schilkp/Fets_and_Crosses/ECAD/EngineTest/EngineTest.sch

## KiCad design ECAD/EngineTest/EngineTest.sch (2021-05-23)

Schematic: EngineTest.sch

Parts:
C1, C2, C3, C4, C7, C9, C10, C11, C12: 0u1; C_0603_1608Metric
C5: 10n; C_0603_1608Metric
C6: 1u; C_0603_1608Metric
C8: 4u7; C_0603_1608Metric
D3: LED; LED_0603_1608Metric
D4: PWR LED; LED_0603_1608Metric
J1: 5V_in; PinHeader_1x02_P2.54mm_Vertical
J2: USB_B_Micro; USB_Mini-B_Wuerth_65100516121_Horizontal
J3: ARM_SWD; PinHeader_2x05_P1.27mm_Vertical
J4: P1; PinSocket_1x10_P2.54mm_Horizontal
J5: P2; PinSocket_1x10_P2.54mm_Horizontal
J6: MOVE; PinSocket_1x10_P2.54mm_Horizontal
J7: PWR; PinSocket_1x10_P2.54mm_Horizontal
JP1: 5V Select; SolderJumper-3_P1.3mm_Open_RoundedPad1.0x1.5mm
R1, R2, R5: 10K; R_0603_1608Metric
R6, R7: rled; R_0603_1608Metric
U1: STM32F030K6Tx; LQFP-32_7x7mm_P0.8mm
U2: FT232RL; SSOP-28_5.3x10.2mm_P0.65mm
U3, U4, U5: 74HCT595PW; TSSOP-16_4.4x5mm_P0.65mm
