schilkp/Fets_and_Crosses/ECAD/Engine/KiCad/Engine.sch

## KiCad design ECAD/Engine/KiCad/Engine.sch (2022-02-07)

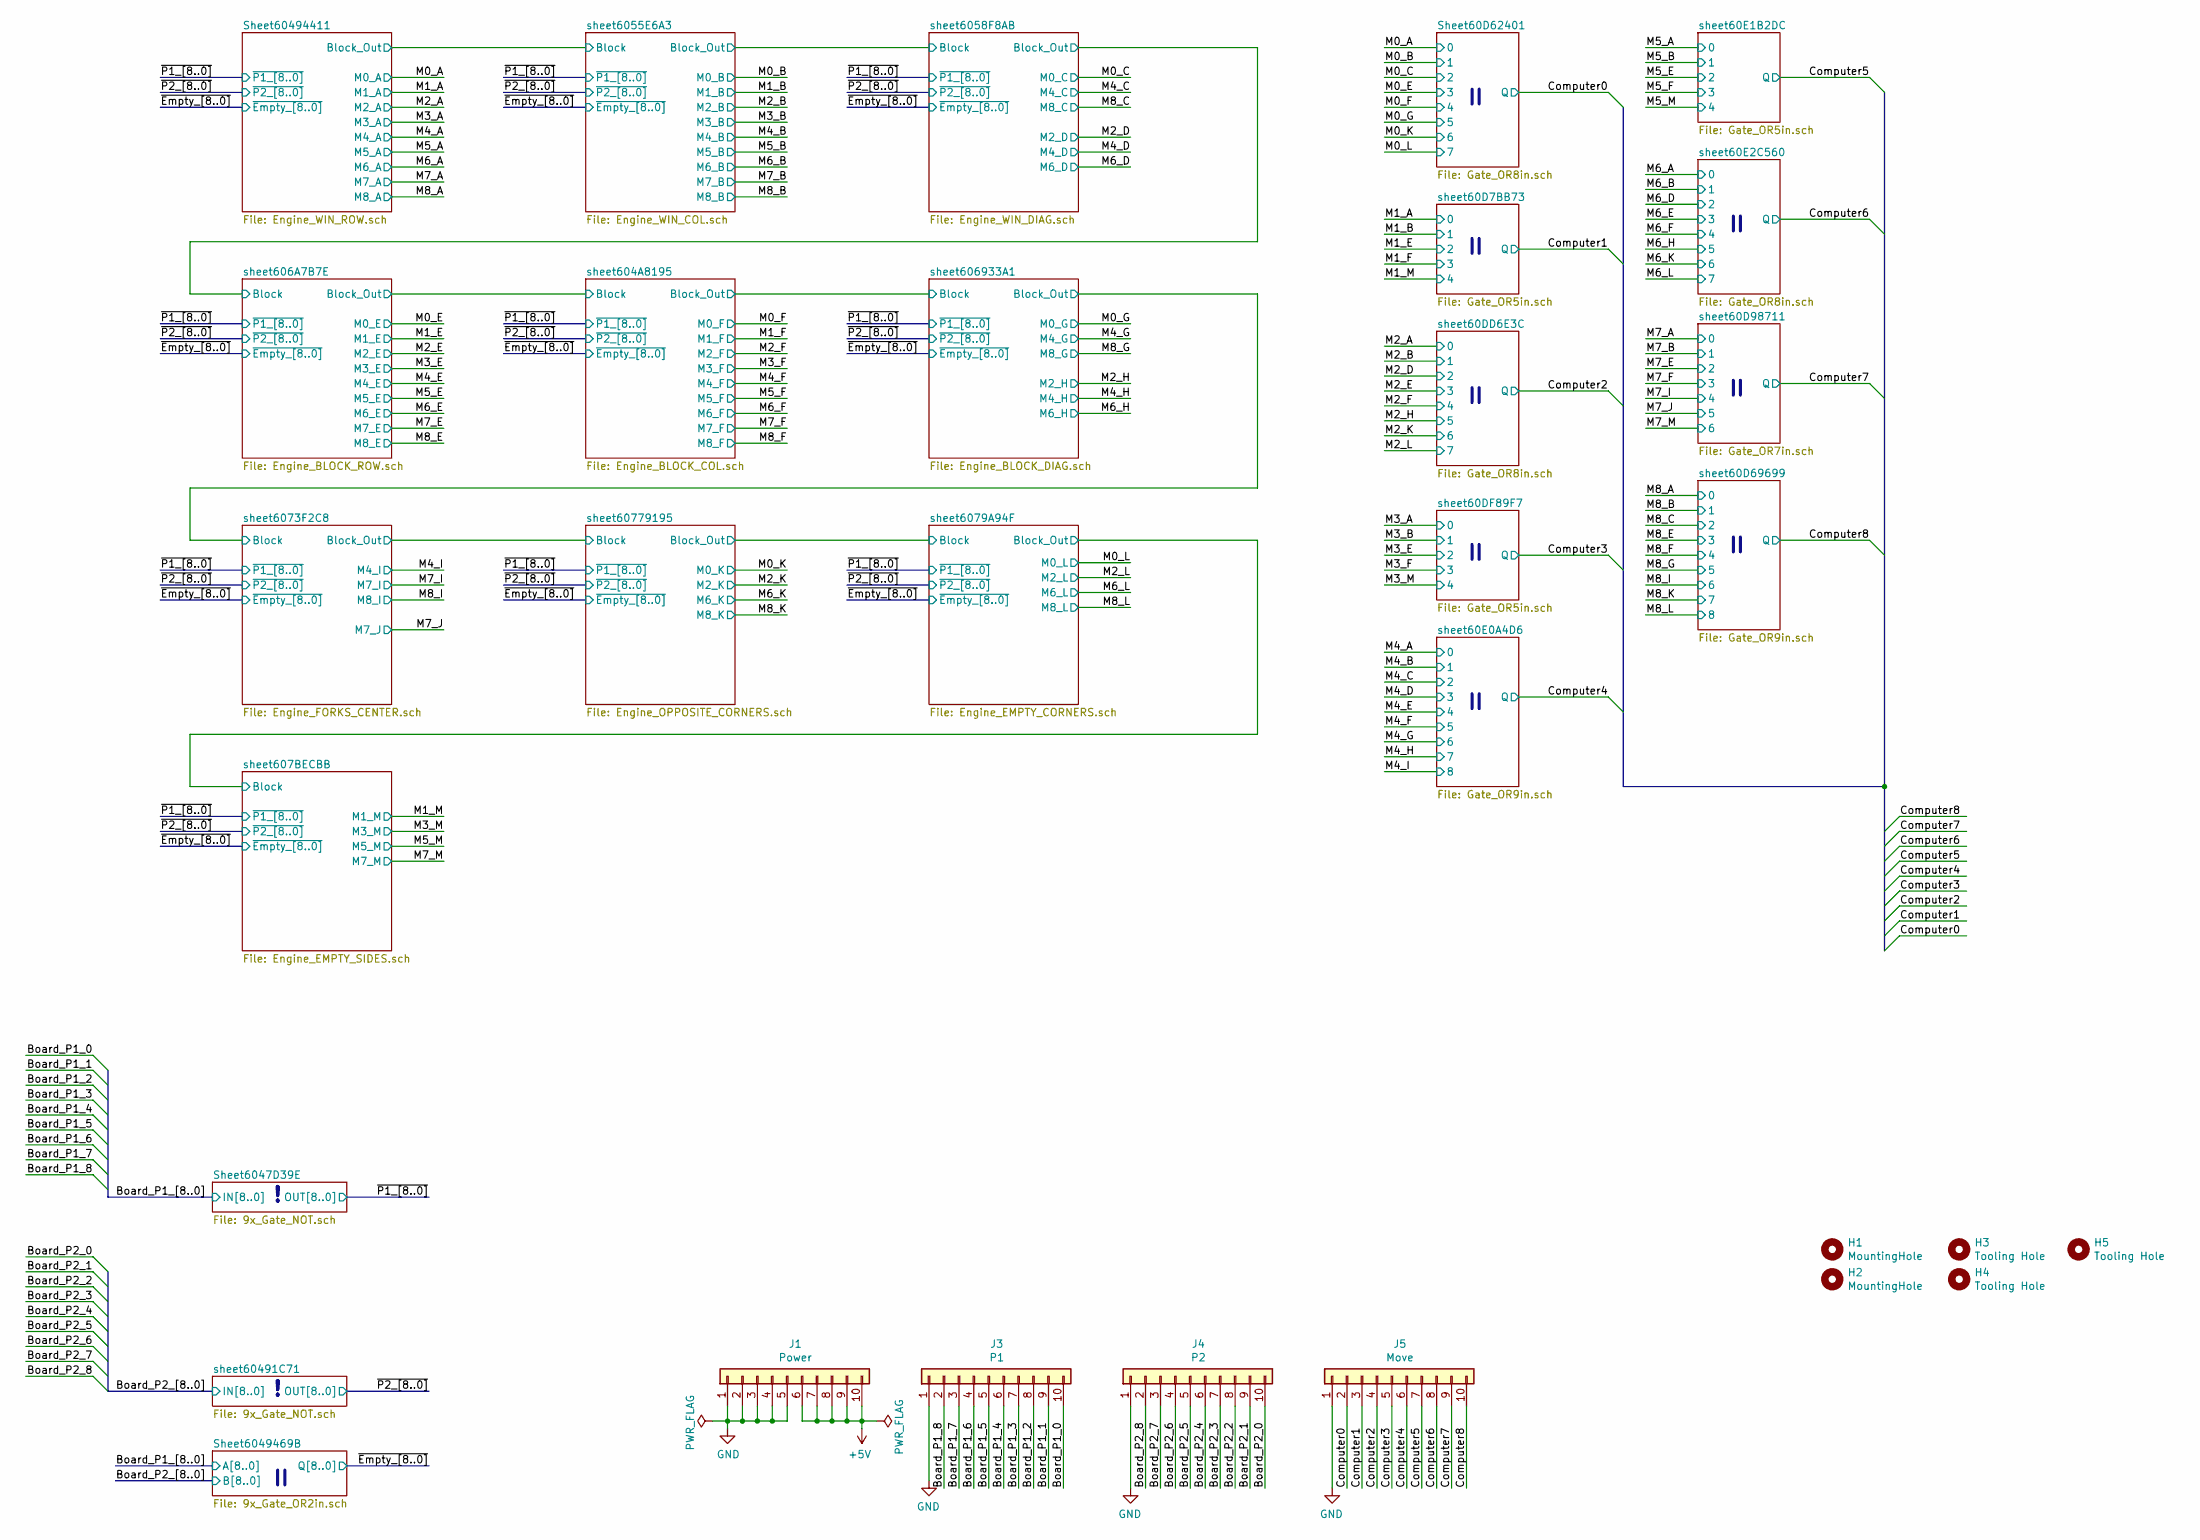
[picture p207: schematic Engine.sch]

Parts:
H1, H2: MountingHole; MountingHole_3.2mm_M3_Pad_Via
H3, H4, H5: Tooling Hole; jlcpcb_tooling_hole
J1: Power; PinHeader_1x10_P2.54mm_Vertical
J3: P1; PinHeader_1x10_P2.54mm_Vertical
J4: P2; PinHeader_1x10_P2.54mm_Vertical
J5: Move; PinHeader_1x10_P2.54mm_Vertical

Connections:
+5V: J1.6, J1.7, J1.8, J1.9, J1.10
Board_P1_0: J3.10
Board_P1_1: J3.9
Board_P1_2: J3.8
Board_P1_3: J3.7
Board_P1_4: J3.6
Board_P1_5: J3.5
Board_P1_6: J3.4
Board_P1_7: J3.3
Board_P1_8: J3.2
Board_P2_0: J4.10
Board_P2_1: J4.9
Board_P2_2: J4.8
Board_P2_3: J4.7
Board_P2_4: J4.6
Board_P2_5: J4.5
Board_P2_6: J4.4
Board_P2_7: J4.3
Board_P2_8: J4.2
Computer0: J5.2
Computer1: J5.3
Computer2: J5.4
Computer3: J5.5
Computer4: J5.6
Computer5: J5.7
Computer6: J5.8
Computer7: J5.9
Computer8: J5.10
GND: J1.1, J1.2, J1.3, J1.4, J1.5, J3.1, J4.1, J5.1
