schilkp/Fets_and_Crosses/ECAD/Engine/KiCad/Gate_NAND2in.sch

## KiCad design ECAD/Engine/KiCad/Gate_NAND2in.sch (2021-03-06)

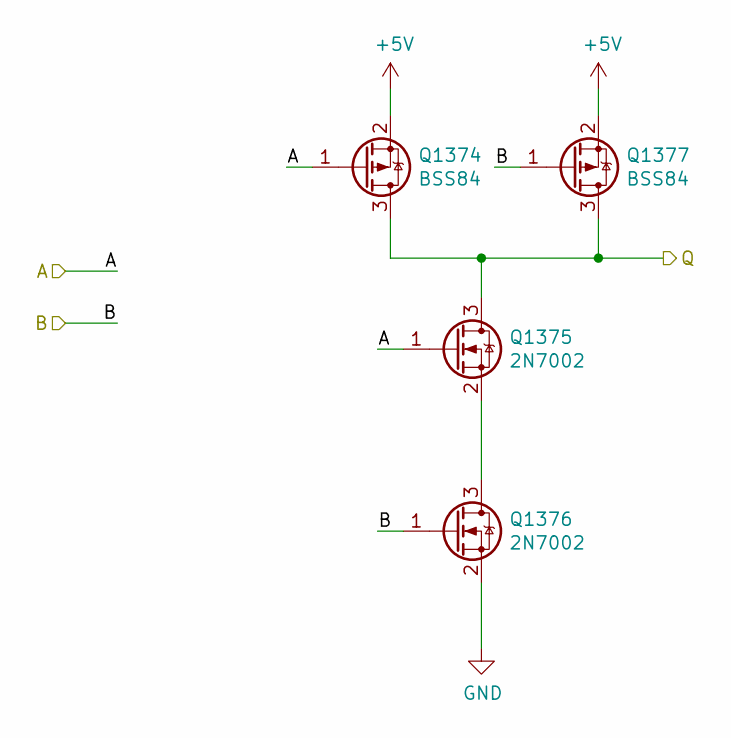
[picture p208: schematic Gate_NAND2in.sch]

Parts:
Q771, Q774: BSS84; SOT-23-P
Q772, Q773: 2N7002; SOT-23-N

Connections:
+5V: Q771.2 (S), Q774.2 (S)
A: Q771.1 (G), Q772.1 (G)
B: Q773.1 (G), Q774.1 (G)
GND: Q773.2 (S)
unnamed: Q772.2 (S), Q773.3 (D)
Q: Q771.3 (D), Q772.3 (D), Q774.3 (D)
