schilkp/Fets_and_Crosses/ECAD/Engine/KiCad/Gate_NOR2in.sch

## KiCad design ECAD/Engine/KiCad/Gate_NOR2in.sch (2022-02-07)

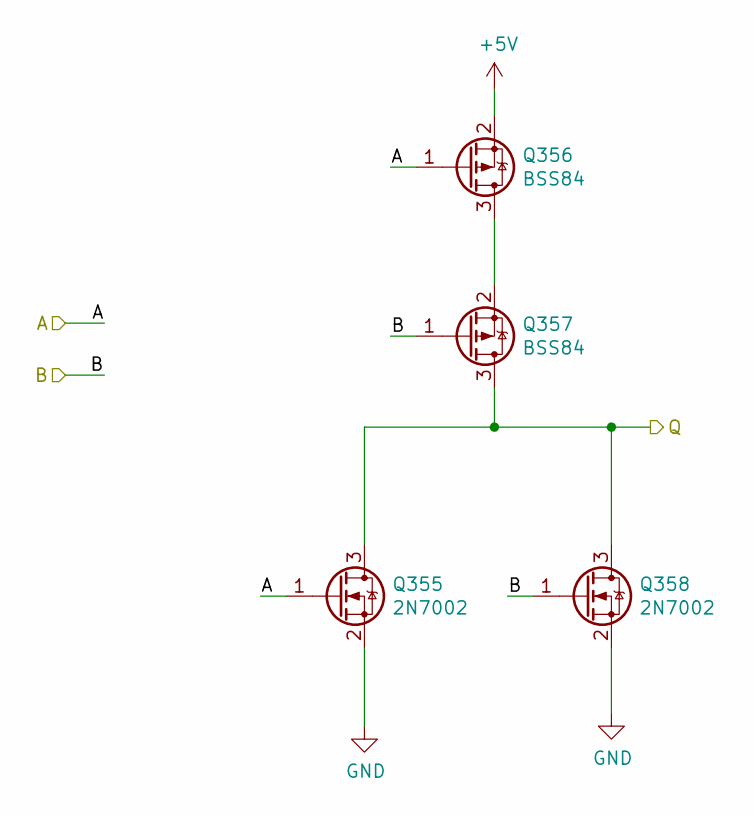
[picture p209: schematic Gate_NOR2in.sch]

Parts:
Q493, Q496: 2N7002; SOT-23-N; LCSC C8545
Q494, Q495: BSS84; SOT-23-P; LCSC C114481

Connections:
+5V: Q494.2 (S)
A: Q493.1 (G), Q494.1 (G)
B: Q495.1 (G), Q496.1 (G)
GND: Q493.2 (S), Q496.2 (S)
unnamed: Q494.3 (D), Q495.2 (S)
Q: Q493.3 (D), Q495.3 (D), Q496.3 (D)
