schilkp/Fets_and_Crosses/ECAD/Engine/KiCad/Gate_NOR3in.sch

## KiCad design ECAD/Engine/KiCad/Gate_NOR3in.sch (2022-02-07)

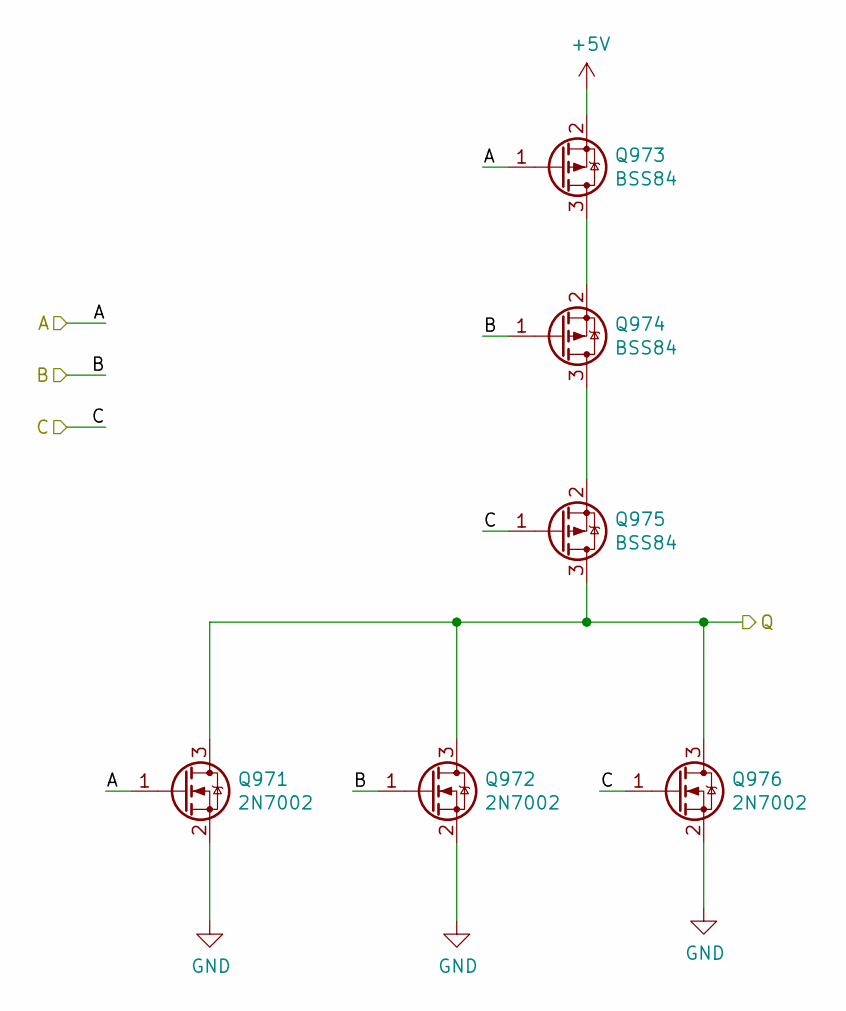
[picture p210: schematic Gate_NOR3in.sch]

Parts:
Q421, Q422, Q426: 2N7002; SOT-23-N; LCSC C8545
Q423, Q424, Q425: BSS84; SOT-23-P; LCSC C114481

Connections:
+5V: Q423.2 (S)
A: Q421.1 (G), Q423.1 (G)
B: Q422.1 (G), Q424.1 (G)
C: Q425.1 (G), Q426.1 (G)
GND: Q421.2 (S), Q422.2 (S), Q426.2 (S)
unnamed: Q423.3 (D), Q424.2 (S)
unnamed: Q424.3 (D), Q425.2 (S)
Q: Q421.3 (D), Q422.3 (D), Q425.3 (D), Q426.3 (D)
