schilkp/Fets_and_Crosses/ECAD/Engine/KiCad/Gate_NOR4in.sch

## KiCad design ECAD/Engine/KiCad/Gate_NOR4in.sch (2022-02-07)

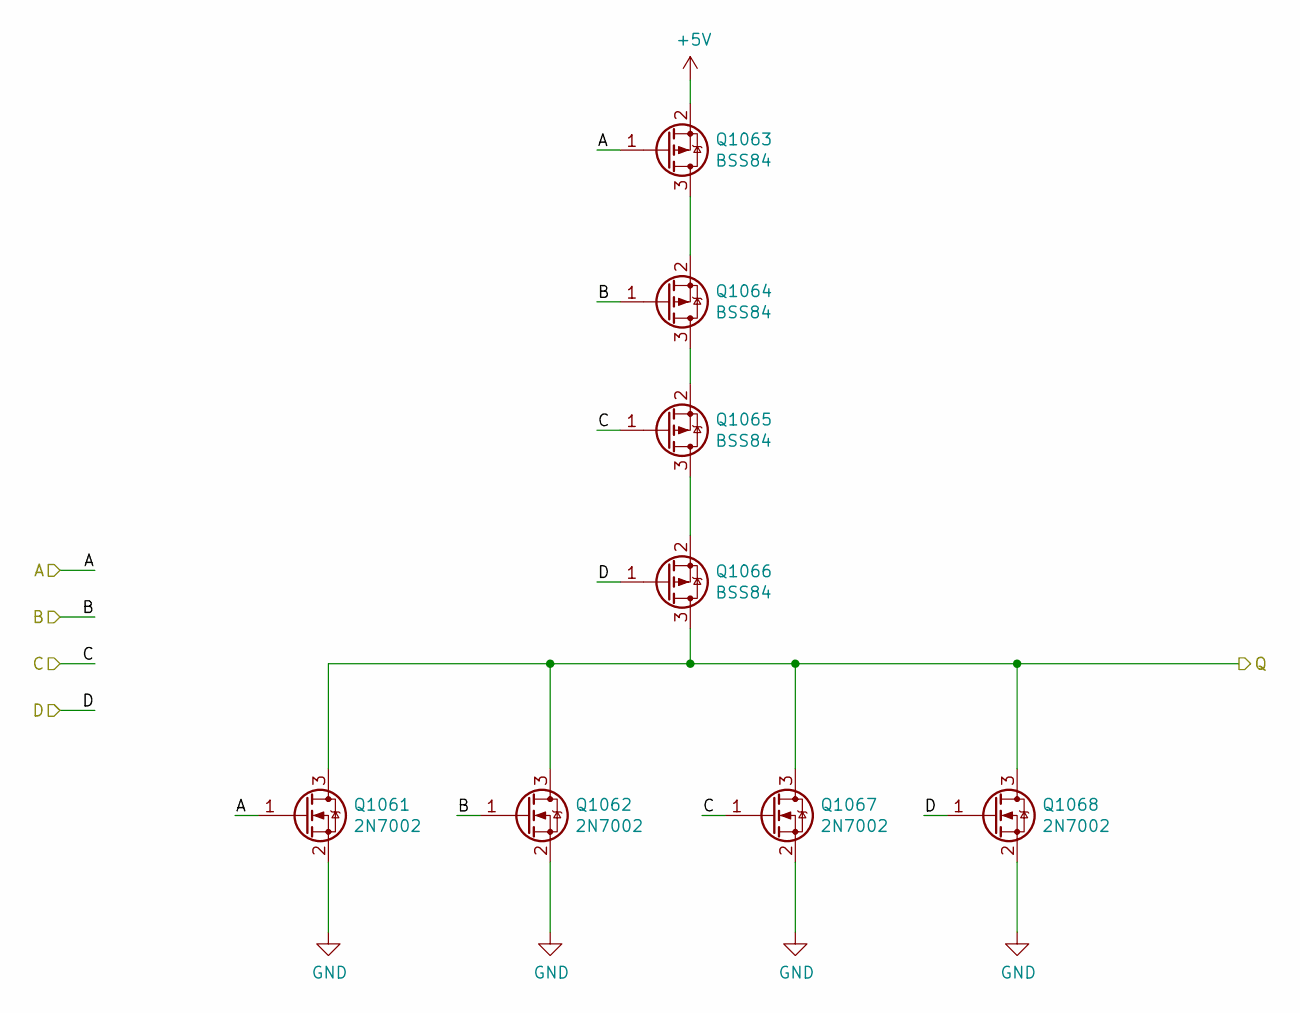
[picture p211: schematic Gate_NOR4in.sch]

Parts:
Q359, Q360, Q365, Q366: 2N7002; SOT-23-N; LCSC C8545
Q361, Q362, Q363, Q364: BSS84; SOT-23-P; LCSC C114481

Connections:
+5V: Q361.2 (S)
A: Q359.1 (G), Q361.1 (G)
B: Q360.1 (G), Q362.1 (G)
C: Q363.1 (G), Q365.1 (G)
D: Q364.1 (G), Q366.1 (G)
GND: Q359.2 (S), Q360.2 (S), Q365.2 (S), Q366.2 (S)
unnamed: Q361.3 (D), Q362.2 (S)
unnamed: Q362.3 (D), Q363.2 (S)
unnamed: Q363.3 (D), Q364.2 (S)
Q: Q359.3 (D), Q360.3 (D), Q364.3 (D), Q365.3 (D), Q366.3 (D)
