schilkp/Fets_and_Crosses/ECAD/Engine/KiCad/Gate_NOR7in.sch

## KiCad design ECAD/Engine/KiCad/Gate_NOR7in.sch (2022-02-07)

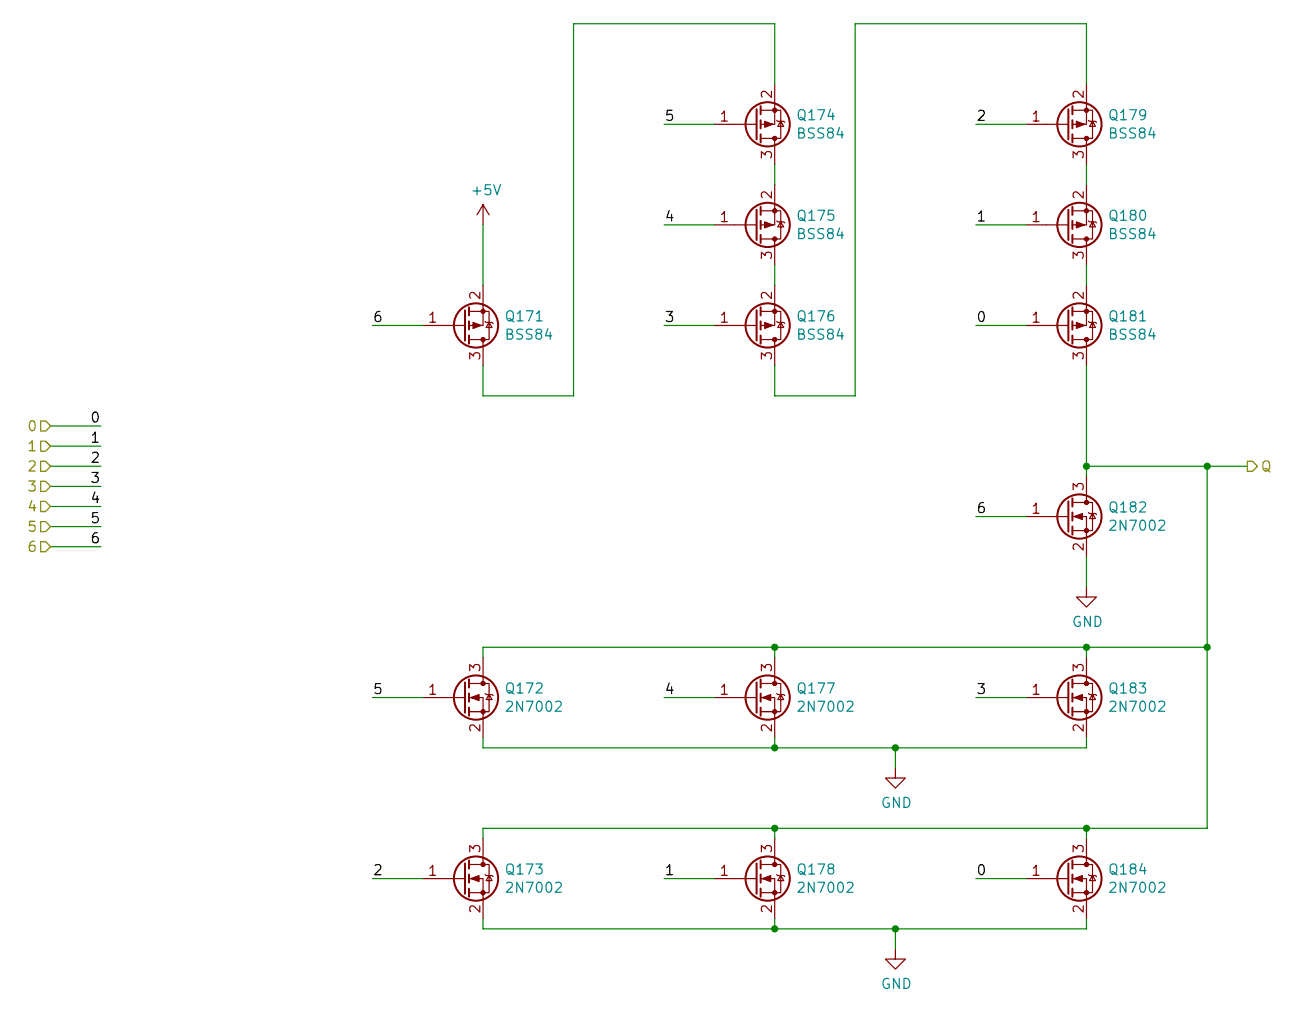
[picture p213: schematic Gate_NOR7in.sch]

Parts:
Q1347, Q1350, Q1351, Q1352, Q1356, Q1357, Q1358: BSS84; SOT-23-P; LCSC C114481
Q1348, Q1349, Q1354, Q1355, Q1359, Q1360, Q1361: 2N7002; SOT-23-N; LCSC C8545

Connections:
0: Q1358.1 (G), Q1361.1 (G)
1: Q1355.1 (G), Q1357.1 (G)
2: Q1349.1 (G), Q1356.1 (G)
3: Q1352.1 (G), Q1360.1 (G)
4: Q1351.1 (G), Q1354.1 (G)
5: Q1348.1 (G), Q1350.1 (G)
6: Q1347.1 (G), Q1359.1 (G)
+5V: Q1347.2 (S)
GND: Q1348.2 (S), Q1349.2 (S), Q1354.2 (S), Q1355.2 (S), Q1359.2 (S), Q1360.2 (S), Q1361.2 (S)
unnamed: Q1347.3 (D), Q1350.2 (S)
unnamed: Q1350.3 (D), Q1351.2 (S)
unnamed: Q1351.3 (D), Q1352.2 (S)
unnamed: Q1352.3 (D), Q1356.2 (S)
unnamed: Q1356.3 (D), Q1357.2 (S)
unnamed: Q1357.3 (D), Q1358.2 (S)
Q: Q1348.3 (D), Q1349.3 (D), Q1354.3 (D), Q1355.3 (D), Q1358.3 (D), Q1359.3 (D), Q1360.3 (D), Q1361.3 (D)
