schilkp/Fets_and_Crosses/ECAD/Engine/KiCad/Gate_NOR9in.sch

## KiCad design ECAD/Engine/KiCad/Gate_NOR9in.sch (2022-02-07)

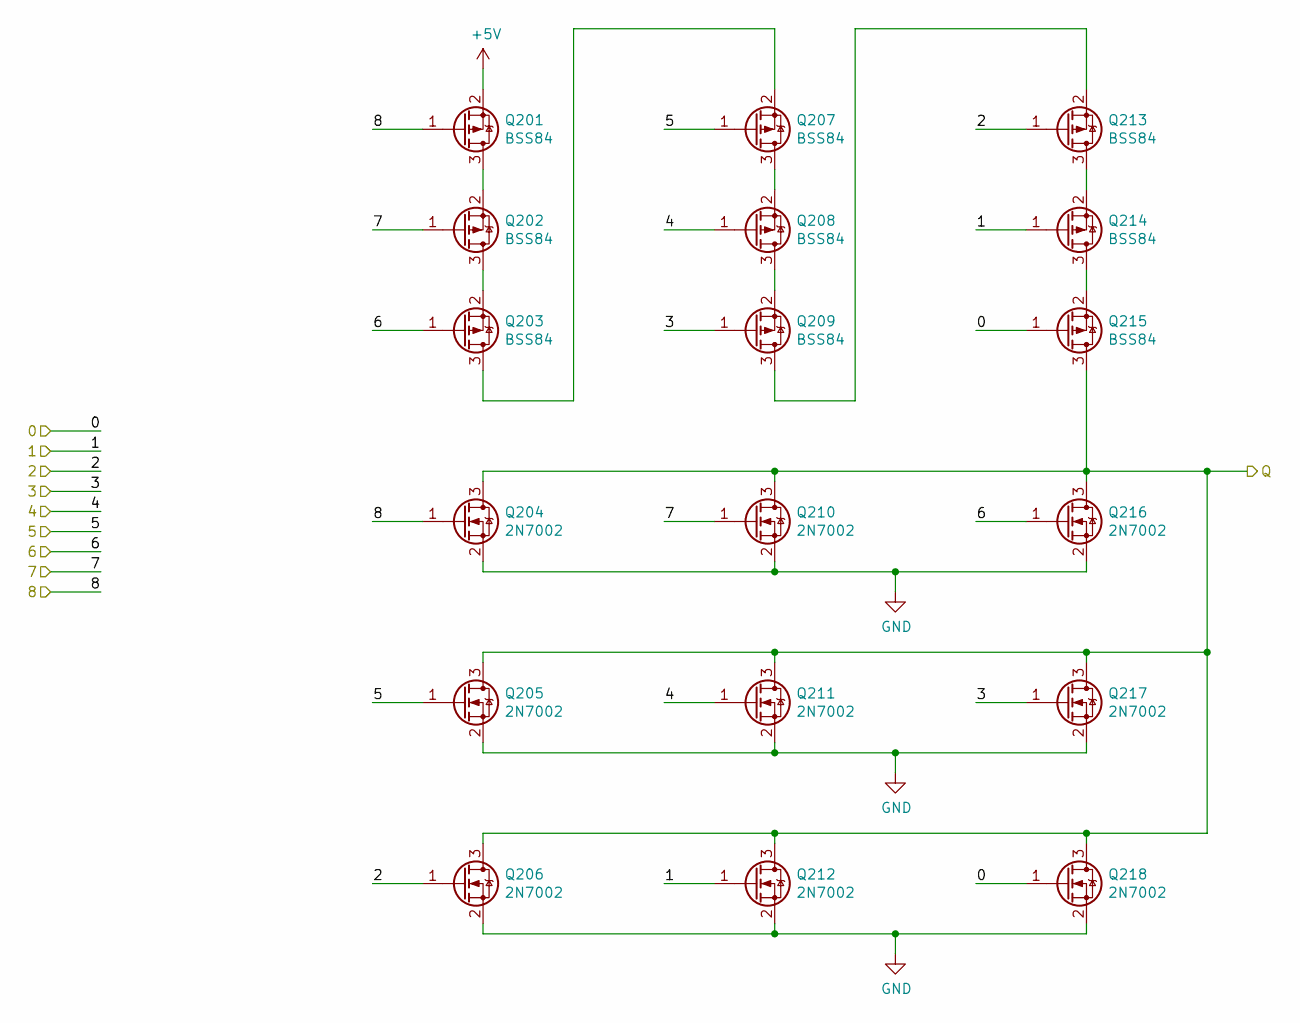
[picture p214: schematic Gate_NOR9in.sch]

Parts:
Q497, Q498, Q499, Q503, Q504, Q505, Q509, Q510, Q511: BSS84; SOT-23-P; LCSC C114481
Q500, Q501, Q502, Q506, Q507, Q508, Q512, Q513, Q514: 2N7002; SOT-23-N; LCSC C8545

Connections:
0: Q511.1 (G), Q514.1 (G)
1: Q508.1 (G), Q510.1 (G)
2: Q502.1 (G), Q509.1 (G)
3: Q505.1 (G), Q513.1 (G)
4: Q504.1 (G), Q507.1 (G)
5: Q501.1 (G), Q503.1 (G)
6: Q499.1 (G), Q512.1 (G)
7: Q498.1 (G), Q506.1 (G)
8: Q497.1 (G), Q500.1 (G)
+5V: Q497.2 (S)
GND: Q500.2 (S), Q501.2 (S), Q502.2 (S), Q506.2 (S), Q507.2 (S), Q508.2 (S), Q512.2 (S), Q513.2 (S), Q514.2 (S)
unnamed: Q497.3 (D), Q498.2 (S)
unnamed: Q498.3 (D), Q499.2 (S)
unnamed: Q499.3 (D), Q503.2 (S)
unnamed: Q503.3 (D), Q504.2 (S)
unnamed: Q504.3 (D), Q505.2 (S)
unnamed: Q505.3 (D), Q509.2 (S)
unnamed: Q509.3 (D), Q510.2 (S)
unnamed: Q510.3 (D), Q511.2 (S)
Q: Q500.3 (D), Q501.3 (D), Q502.3 (D), Q506.3 (D), Q507.3 (D), Q508.3 (D), Q511.3 (D), Q512.3 (D), Q513.3 (D), Q514.3 (D)
