schilkp/Fets_and_Crosses/ECAD/Engine/KiCad/Gate_NOT.sch

## KiCad design ECAD/Engine/KiCad/Gate_NOT.sch (2022-02-07)

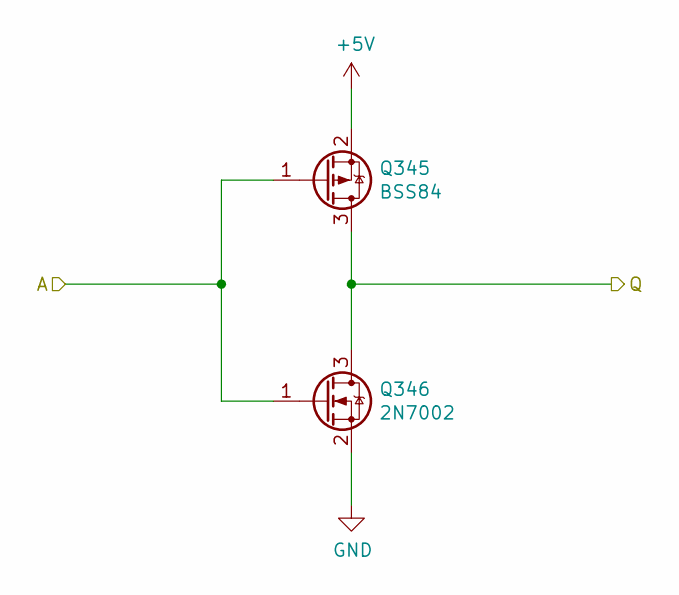
[picture p215: schematic Gate_NOT.sch]

Parts:
Q427: BSS84; SOT-23-P; LCSC C114481
Q428: 2N7002; SOT-23-N; LCSC C8545

Connections:
+5V: Q427.2 (S)
A: Q427.1 (G), Q428.1 (G)
GND: Q428.2 (S)
Q: Q427.3 (D), Q428.3 (D)
