schilkp/Fets_and_Crosses/ECAD/Fets_and_Crosses/KiCad/Clock.sch

## KiCad design ECAD/Fets_and_Crosses/KiCad/Clock.sch (2022-02-07)

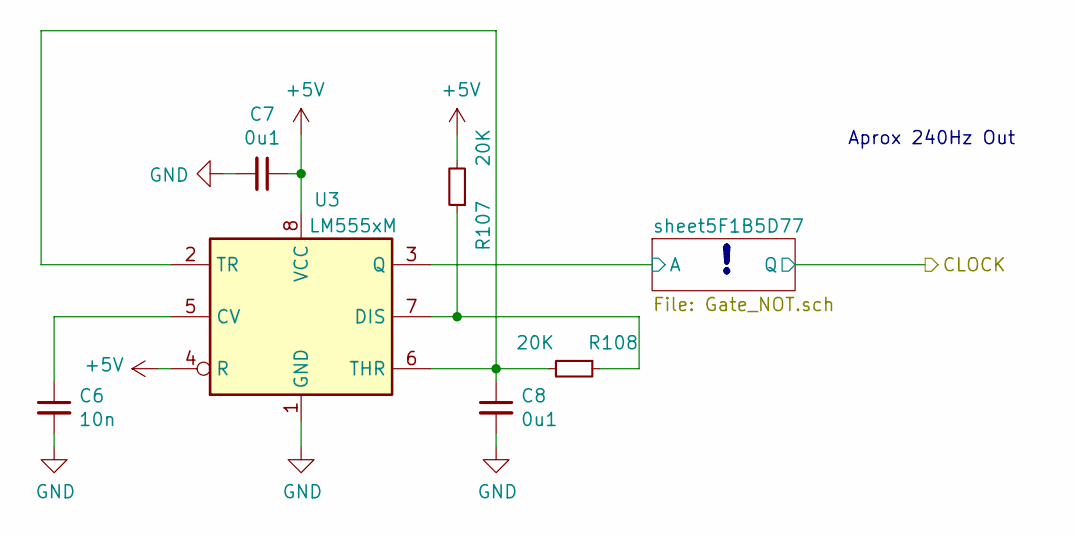
[picture p216: schematic Clock.sch]

Parts:
C6: 10n; C_0603_1608Metric; LCSC C57112
C7, C8: 0u1; C_0603_1608Metric_NOLBL; LCSC C14663
R107, R108: 20K; R_0603_1608Metric_NOLBL; LCSC C4184
U3: LM555xM; SOIC-8_3.9x4.9mm_P1.27mm; LCSC C7593

Connections:
+5V: C7.1, R107.2, U3.4 (R), U3.8 (VCC)
A: U3.3 (Q)
GND: C6.2, C7.2, C8.2, U3.1 (GND)
unnamed: C6.1, U3.5 (CV)
unnamed: C8.1, R108.2, U3.2 (TR), U3.6 (THR)
unnamed: R107.1, R108.1, U3.7 (DIS)

Notes on the sheet:
Aprox 240Hz Out
