schilkp/Fets_and_Crosses/ECAD/Fets_and_Crosses/KiCad/Computer.sch

## KiCad design ECAD/Fets_and_Crosses/KiCad/Computer.sch (2022-02-07)

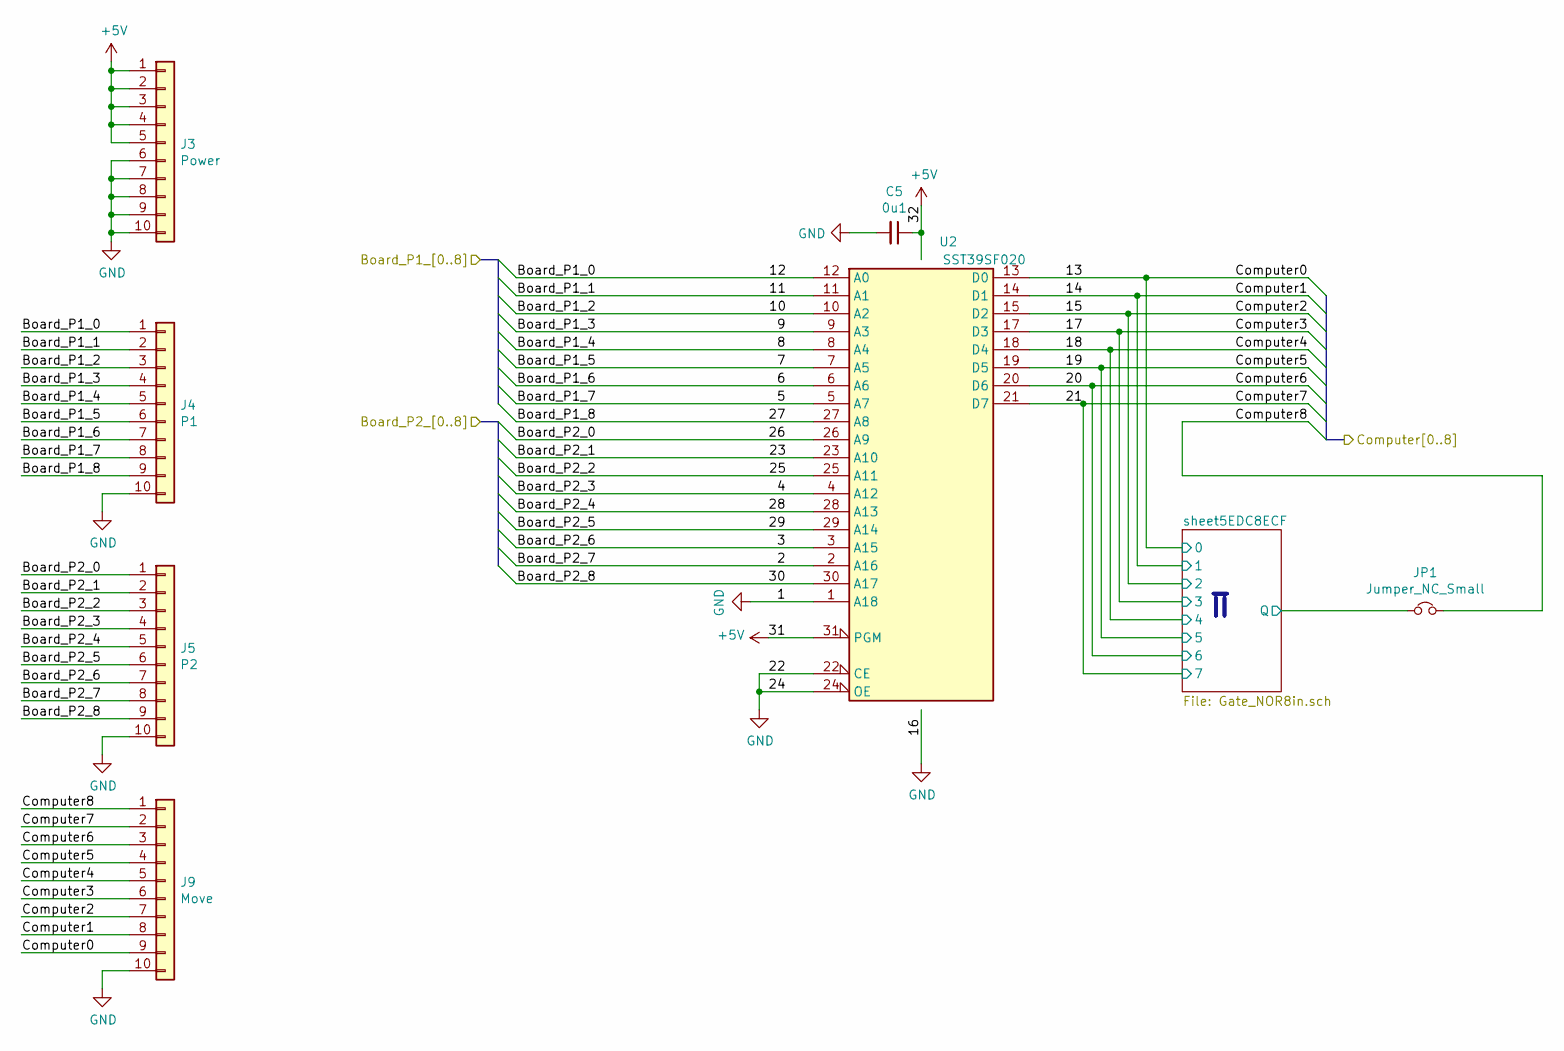
[picture p217: schematic Computer.sch]

Parts:
C5: 0u1; C_0603_1608Metric_NOLBL; LCSC C14663
J3: Power; PinSocket_1x10_P2.54mm_Horizontal
J4: P1; PinSocket_1x10_P2.54mm_Horizontal
J5: P2; PinSocket_1x10_P2.54mm_Horizontal
J9: Move; PinSocket_1x10_P2.54mm_Horizontal
JP1: Jumper_NC_Small; R_0603_1608Metric
U2: SST39SF020; PLCC-32_11.4x14.0mm_P1.27mm_SMD-Socket

Connections:
2: J5.8, U2.2 (A16)
3: J5.7, U2.3 (A15)
4: J5.4, U2.4 (A12)
5: J4.8, U2.5 (A7)
6: J4.7, U2.6 (A6)
7: J4.6, U2.7 (A5)
8: J4.5, U2.8 (A4)
9: J4.4, U2.9 (A3)
10: J4.3, U2.10 (A2)
11: J4.2, U2.11 (A1)
12: J4.1, U2.12 (A0)
13: J9.9, U2.13 (D0)
14: J9.8, U2.14 (D1)
15: J9.7, U2.15 (D2)
17: J9.6, U2.17 (D3)
18: J9.5, U2.18 (D4)
19: J9.4, U2.19 (D5)
20: J9.3, U2.20 (D6)
21: J9.2, U2.21 (D7)
23: J5.2, U2.23 (A10)
25: J5.3, U2.25 (A11)
26: J5.1, U2.26 (A9)
27: J4.9, U2.27 (A8)
28: J5.5, U2.28 (A13)
29: J5.6, U2.29 (A14)
30: J5.9, U2.30 (A17)
+5V: C5.1, J3.1, J3.2, J3.3, J3.4, J3.5, U2.31 (PGM), U2.32 (VCC)
Computer8: J9.1, JP1.2
GND: C5.2, J3.6, J3.7, J3.8, J3.9, J3.10, J4.10, J5.10, J9.10, U2.1 (A18), U2.16 (GND), U2.22 (CE), U2.24 (OE)
Q: JP1.1

Notes on the sheet:
~II
