schilkp/Fets_and_Crosses/ECAD/Fets_and_Crosses/KiCad/FetsAndCrosses.sch

## KiCad design ECAD/Fets_and_Crosses/KiCad/FetsAndCrosses.sch (2022-02-07)

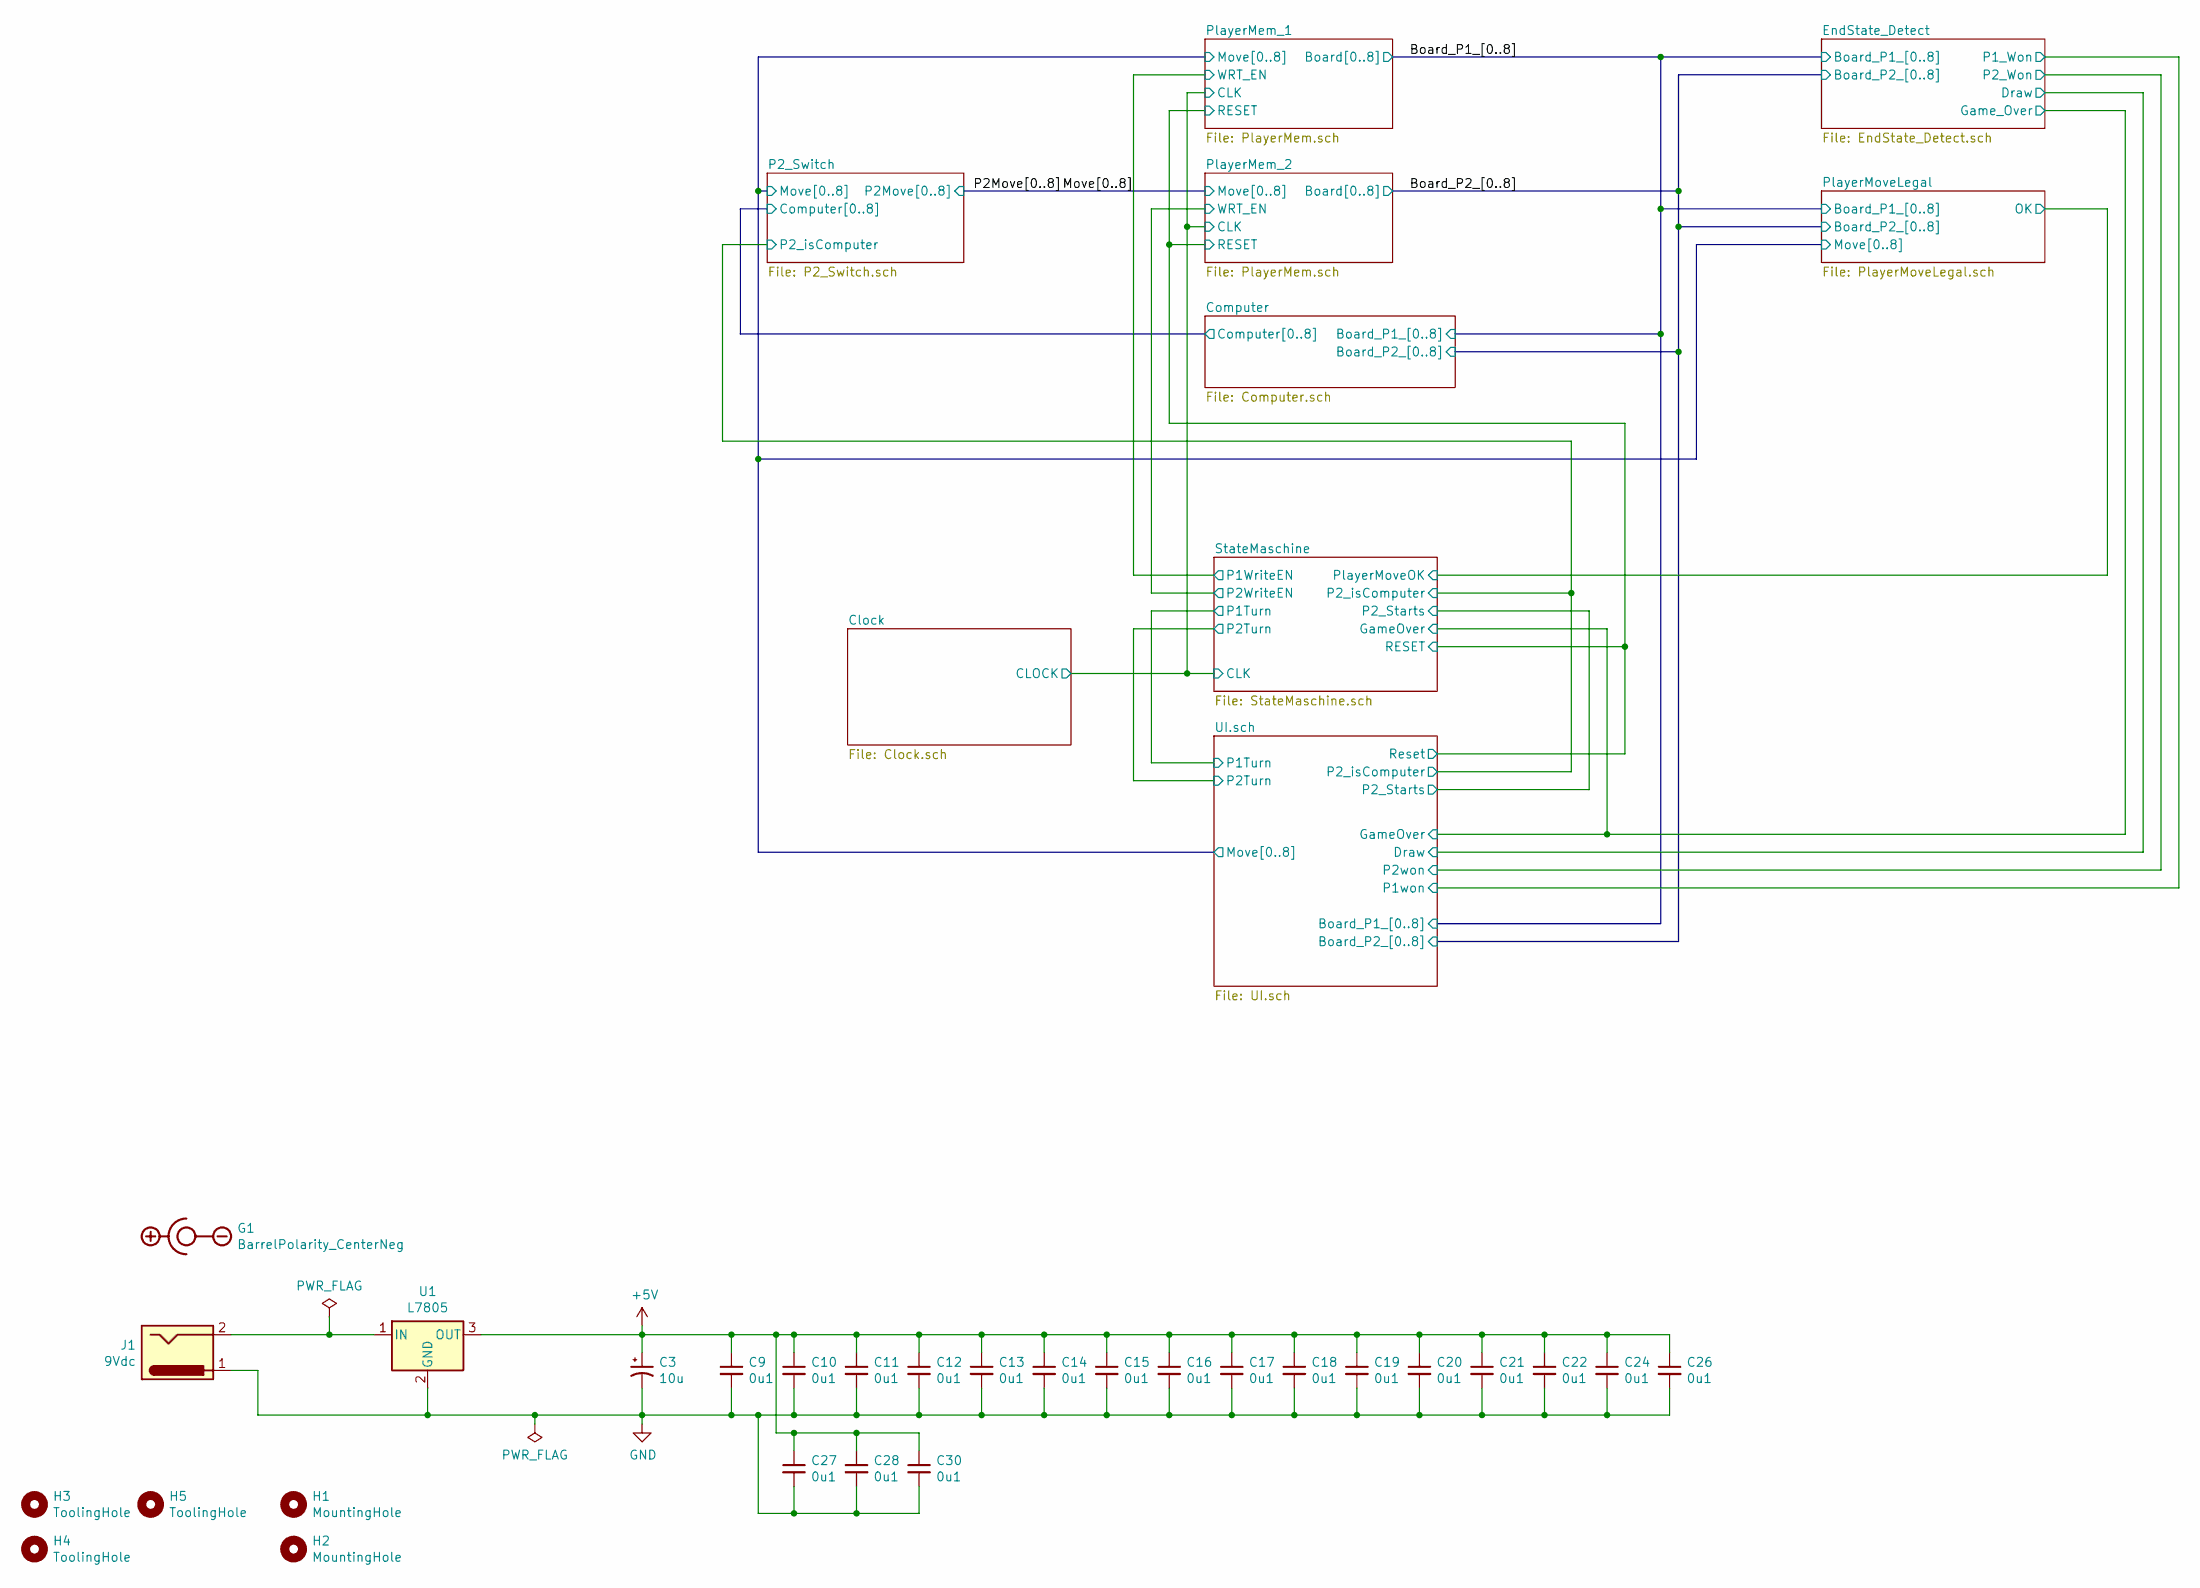
[picture p218: schematic FetsAndCrosses.sch]

Parts:
C3: 10u; CP_Elec_6.3x7.7
C9, C10, C11, C12, C13, C14, C15, C16, C17, C18, C19, C20, C21, C22, C24, C26, C27, C28, C30: 0u1; C_0603_1608Metric_NOLBL; LCSC C14663
G1: BarrelPolarity_CenterNeg; BarrelPolarity_3mm_CenterNeg
H1, H2: MountingHole; MountingHole_3.2mm_M3_Pad_Via
H3, H4, H5: ToolingHole; jlcpcb_tooling_hole
J1: 9Vdc; BarrelJack_Horizontal
U1: L7805; TO-252-2; LCSC C58069

Connections:
+5V: C3.1, C9.1, C10.1, C11.1, C12.1, C13.1, C14.1, C15.1, C16.1, C17.1, C18.1, C19.1, C20.1, C21.1, C22.1, C24.1, C26.1, C27.1, C28.1, C30.1, U1.3 (OUT)
GND: C3.2, C9.2, C10.2, C11.2, C12.2, C13.2, C14.2, C15.2, C16.2, C17.2, C18.2, C19.2, C20.2, C21.2, C22.2, C24.2, C26.2, C27.2, C28.2, C30.2, J1.1, U1.2 (GND)
unnamed: J1.2, U1.1 (IN)
