schilkp/Fets_and_Crosses/ECAD/Fets_and_Crosses/KiCad/Gate_MUX.sch

## KiCad design ECAD/Fets_and_Crosses/KiCad/Gate_MUX.sch (2022-02-07)

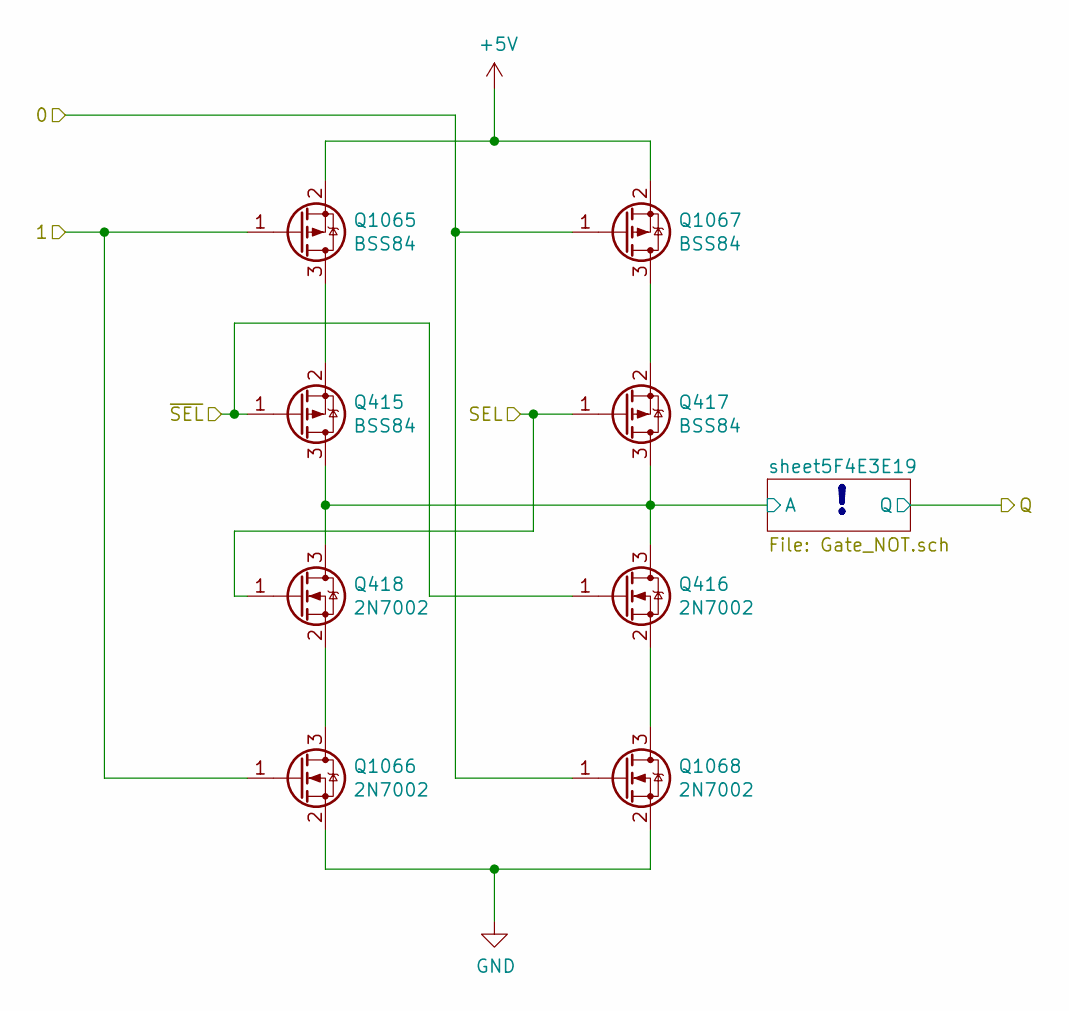
[picture p219: schematic Gate_MUX.sch]

Parts:
Q407, Q409, Q1021, Q1023: BSS84; SOT-23-P; LCSC C114481
Q408, Q410, Q1022, Q1024: 2N7002; SOT-23-N; LCSC C8545

Connections:
0: Q1023.1 (G), Q1024.1 (G)
1: Q1021.1 (G), Q1022.1 (G)
+5V: Q1021.2 (S), Q1023.2 (S)
A: Q407.3 (D), Q408.3 (D), Q409.3 (D), Q410.3 (D)
GND: Q1022.2 (S), Q1024.2 (S)
unnamed: Q407.2 (S), Q1021.3 (D)
unnamed: Q410.2 (S), Q1022.3 (D)
unnamed: Q409.2 (S), Q1023.3 (D)
unnamed: Q408.2 (S), Q1024.3 (D)
SEL: Q409.1 (G), Q410.1 (G)
~SEL: Q407.1 (G), Q408.1 (G)
