schilkp/Fets_and_Crosses/ECAD/Fets_and_Crosses/KiCad/Gate_NAND3in.sch

## KiCad design ECAD/Fets_and_Crosses/KiCad/Gate_NAND3in.sch (2022-02-07)

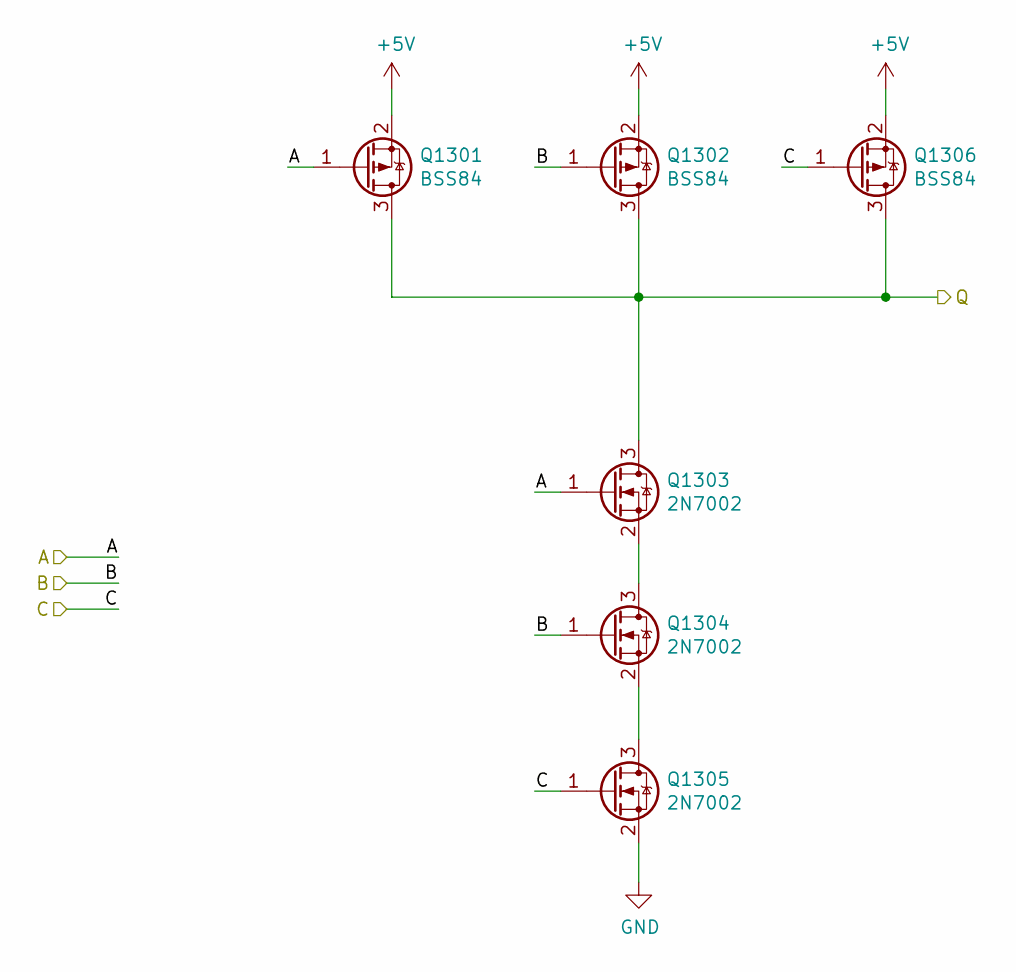
[picture p220: schematic Gate_NAND3in.sch]

Parts:
Q429, Q430, Q434: BSS84; SOT-23-P; LCSC C114481
Q431, Q432, Q433: 2N7002; SOT-23-N; LCSC C8545

Connections:
+5V: Q429.2 (S), Q430.2 (S), Q434.2 (S)
A: Q429.1 (G), Q431.1 (G)
B: Q430.1 (G), Q432.1 (G)
C: Q433.1 (G), Q434.1 (G)
GND: Q433.2 (S)
unnamed: Q431.2 (S), Q432.3 (D)
unnamed: Q432.2 (S), Q433.3 (D)
Q: Q429.3 (D), Q430.3 (D), Q431.3 (D), Q434.3 (D)
