schilkp/Fets_and_Crosses/ECAD/Fets_and_Crosses/KiCad/Gate_NAND8in.sch

## KiCad design ECAD/Fets_and_Crosses/KiCad/Gate_NAND8in.sch (2022-02-07)

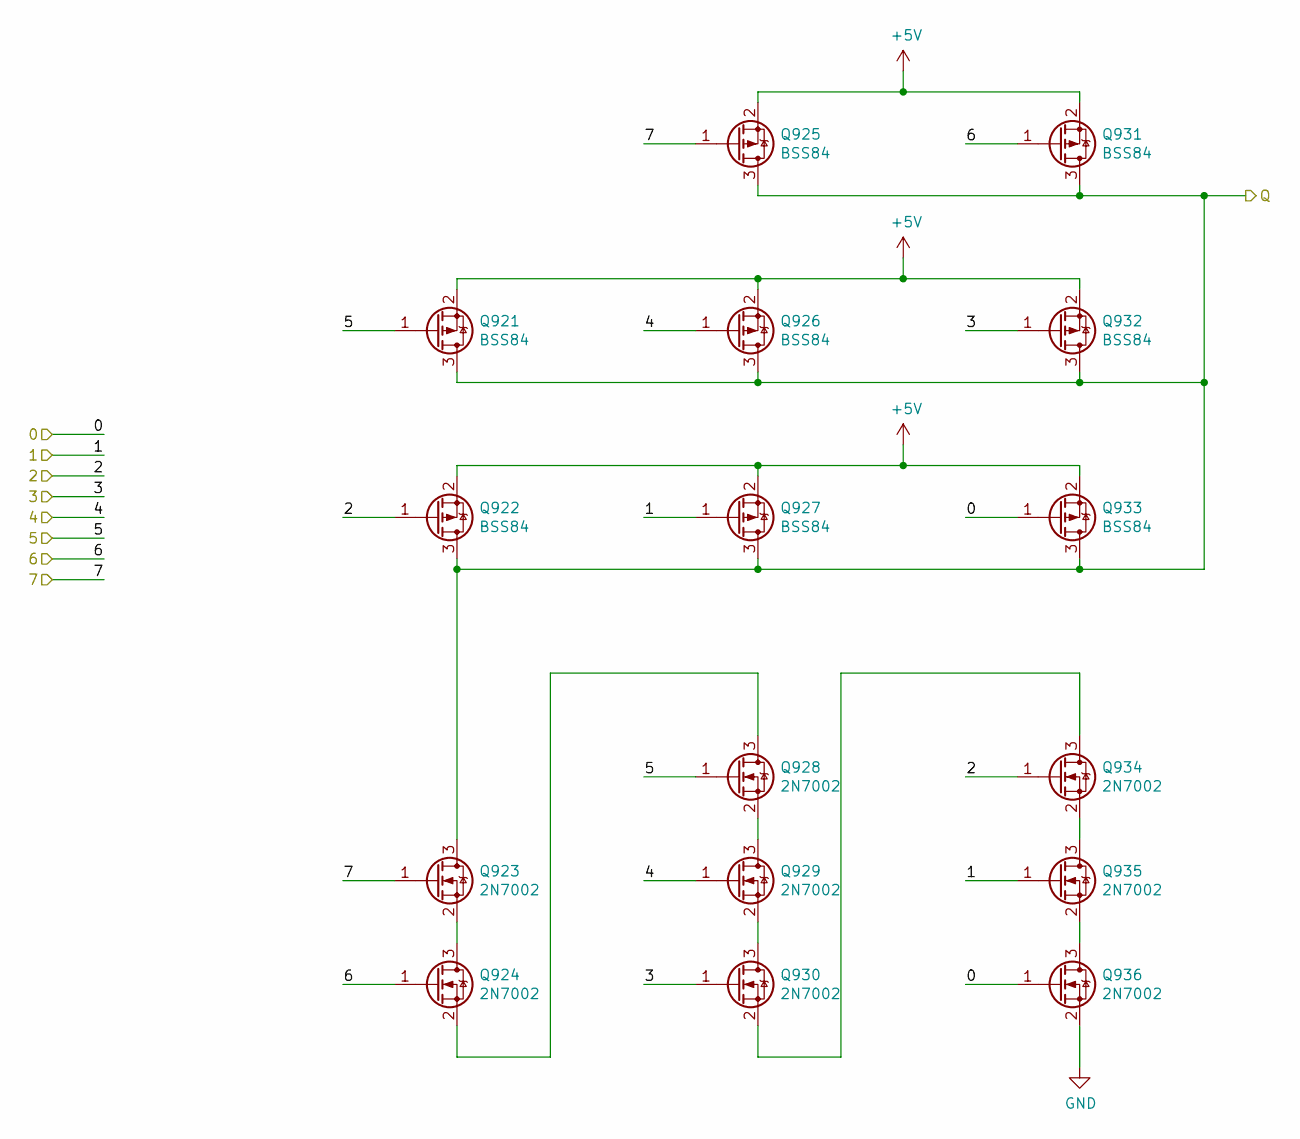
[picture p221: schematic Gate_NAND8in.sch]

Parts:
Q477, Q478, Q481, Q482, Q483, Q487, Q488, Q489: BSS84; SOT-23-P; LCSC C114481
Q479, Q480, Q484, Q485, Q486, Q490, Q491, Q492: 2N7002; SOT-23-N; LCSC C8545

Connections:
0: Q489.1 (G), Q492.1 (G)
1: Q483.1 (G), Q491.1 (G)
2: Q478.1 (G), Q490.1 (G)
3: Q486.1 (G), Q488.1 (G)
4: Q482.1 (G), Q485.1 (G)
5: Q477.1 (G), Q484.1 (G)
6: Q480.1 (G), Q487.1 (G)
7: Q479.1 (G), Q481.1 (G)
+5V: Q477.2 (S), Q478.2 (S), Q481.2 (S), Q482.2 (S), Q483.2 (S), Q487.2 (S), Q488.2 (S), Q489.2 (S)
GND: Q492.2 (S)
unnamed: Q479.2 (S), Q480.3 (D)
unnamed: Q480.2 (S), Q484.3 (D)
unnamed: Q484.2 (S), Q485.3 (D)
unnamed: Q485.2 (S), Q486.3 (D)
unnamed: Q486.2 (S), Q490.3 (D)
unnamed: Q490.2 (S), Q491.3 (D)
unnamed: Q491.2 (S), Q492.3 (D)
Q: Q477.3 (D), Q478.3 (D), Q479.3 (D), Q481.3 (D), Q482.3 (D), Q483.3 (D), Q487.3 (D), Q488.3 (D), Q489.3 (D)
