schilkp/Fets_and_Crosses/ECAD/Fets_and_Crosses/KiCad/Gate_NAND9in.sch

## KiCad design ECAD/Fets_and_Crosses/KiCad/Gate_NAND9in.sch (2022-02-07)

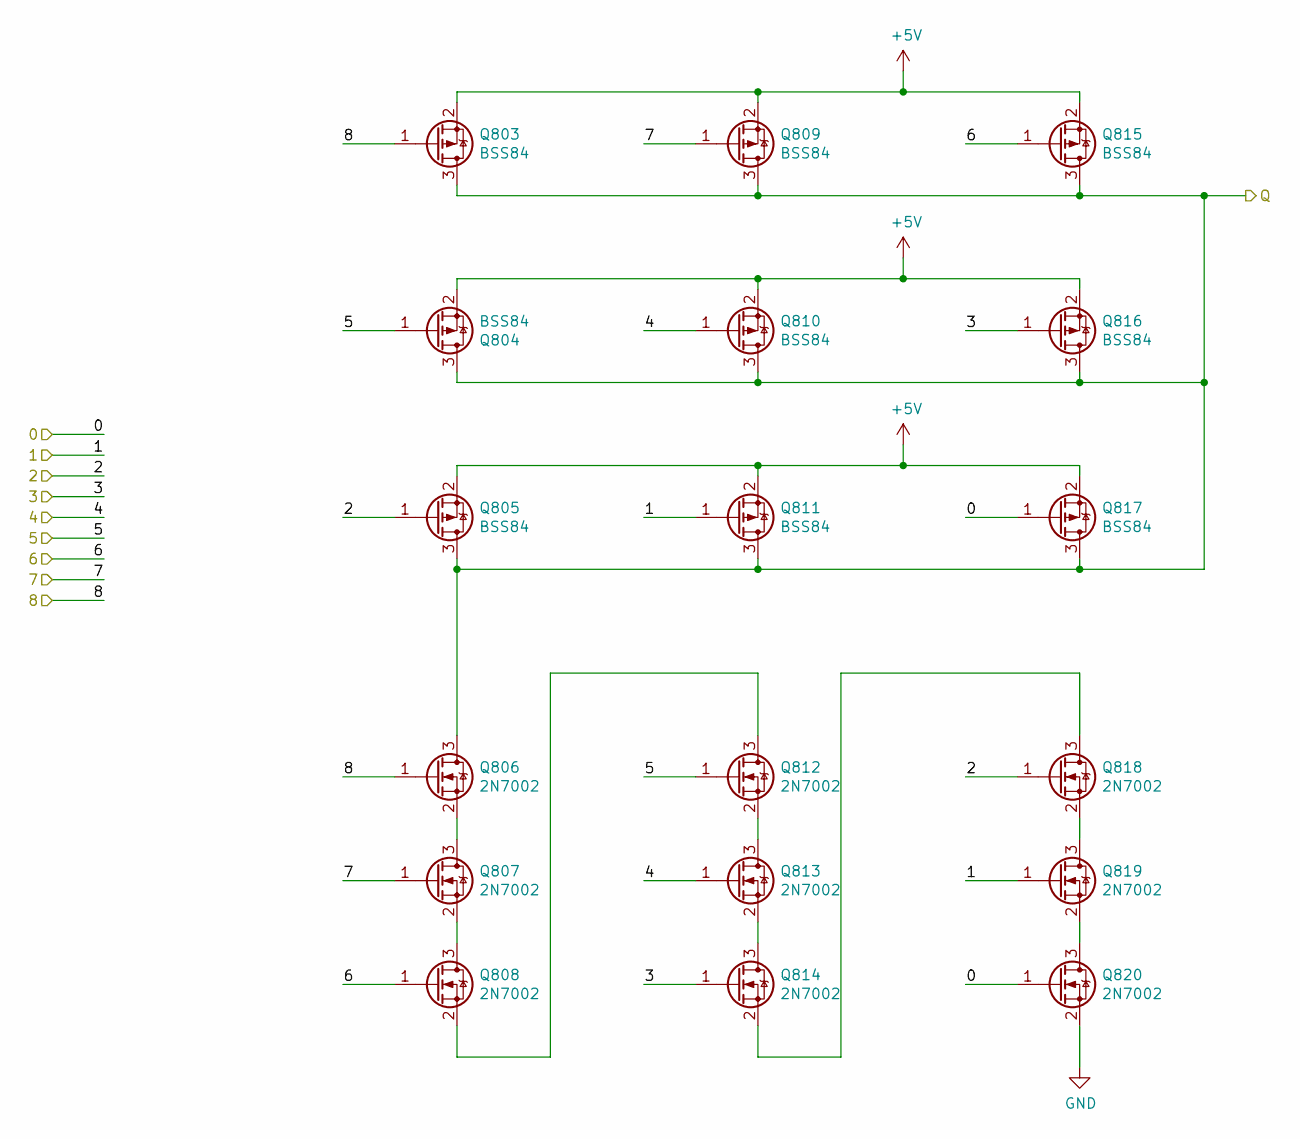
[picture p222: schematic Gate_NAND9in.sch]

Parts:
Q803, Q804, Q805, Q809, Q810, Q811, Q815, Q816, Q817: BSS84; SOT-23-P; LCSC C114481
Q806, Q807, Q808, Q812, Q813, Q814, Q818, Q819, Q820: 2N7002; SOT-23-N; LCSC C8545

Connections:
0: Q817.1 (G), Q820.1 (G)
1: Q811.1 (G), Q819.1 (G)
2: Q805.1 (G), Q818.1 (G)
3: Q814.1 (G), Q816.1 (G)
4: Q810.1 (G), Q813.1 (G)
5: Q804.1 (G), Q812.1 (G)
6: Q808.1 (G), Q815.1 (G)
7: Q807.1 (G), Q809.1 (G)
8: Q803.1 (G), Q806.1 (G)
+5V: Q803.2 (S), Q804.2 (S), Q805.2 (S), Q809.2 (S), Q810.2 (S), Q811.2 (S), Q815.2 (S), Q816.2 (S), Q817.2 (S)
GND: Q820.2 (S)
unnamed: Q806.2 (S), Q807.3 (D)
unnamed: Q807.2 (S), Q808.3 (D)
unnamed: Q808.2 (S), Q812.3 (D)
unnamed: Q812.2 (S), Q813.3 (D)
unnamed: Q813.2 (S), Q814.3 (D)
unnamed: Q814.2 (S), Q818.3 (D)
unnamed: Q818.2 (S), Q819.3 (D)
unnamed: Q819.2 (S), Q820.3 (D)
Q: Q803.3 (D), Q804.3 (D), Q805.3 (D), Q806.3 (D), Q809.3 (D), Q810.3 (D), Q811.3 (D), Q815.3 (D), Q816.3 (D), Q817.3 (D)
