schilkp/Fets_and_Crosses/ECAD/Fets_and_Crosses/KiCad/Gate_SchmittInv.sch

## KiCad design ECAD/Fets_and_Crosses/KiCad/Gate_SchmittInv.sch (2022-02-07)

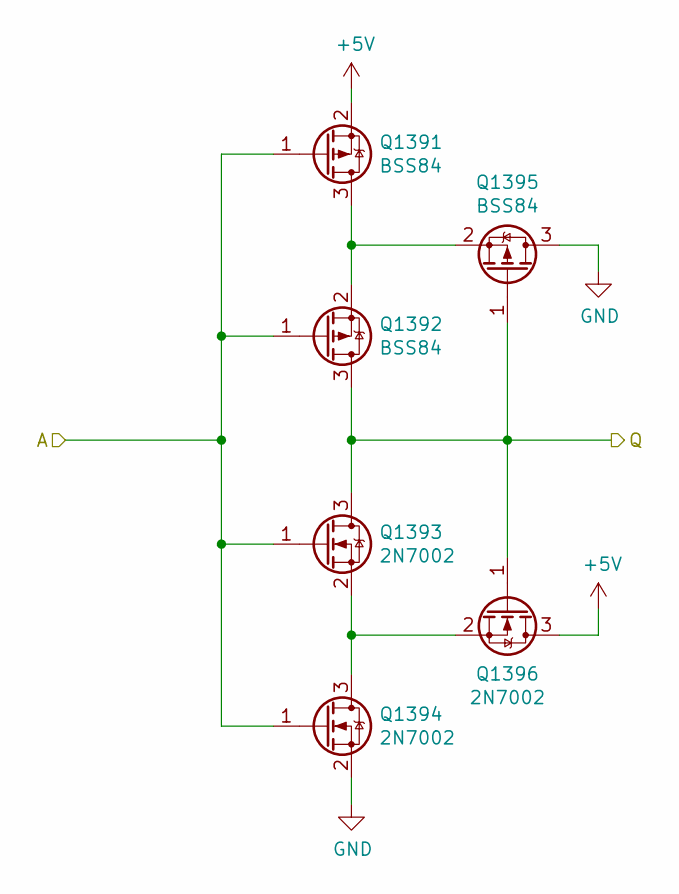
[picture p223: schematic Gate_SchmittInv.sch]

Parts:
Q1391, Q1392, Q1395: BSS84; SOT-23-P; LCSC C114481
Q1393, Q1394, Q1396: 2N7002; SOT-23-N; LCSC C8545

Connections:
+5V: Q1391.2 (S), Q1396.3 (D)
A: Q1391.1 (G), Q1392.1 (G), Q1393.1 (G), Q1394.1 (G)
GND: Q1394.2 (S), Q1395.3 (D)
unnamed: Q1391.3 (D), Q1392.2 (S), Q1395.2 (S)
unnamed: Q1393.2 (S), Q1394.3 (D), Q1396.2 (S)
Q: Q1392.3 (D), Q1393.3 (D), Q1395.1 (G), Q1396.1 (G)
