schilkp/Fets_and_Crosses/ECAD/Fets_and_Crosses/KiCad/UI_BoardLEDCell.sch

## KiCad design ECAD/Fets_and_Crosses/KiCad/UI_BoardLEDCell.sch (2022-02-07)

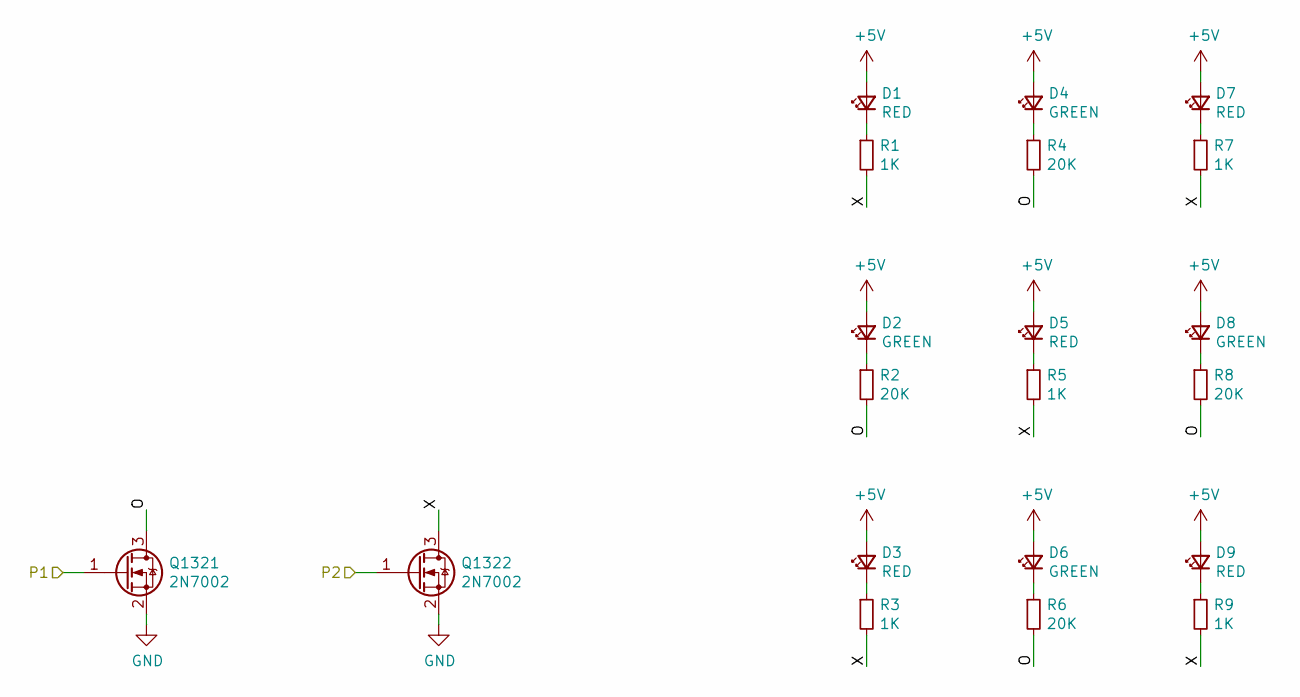
[picture p224: schematic UI_BoardLEDCell.sch]

Parts:
D1, D3, D5, D7, D9: RED; D_0805_2012Metric_NOLBL; LCSC C72037
D2, D4, D6, D8: GREEN; D_0805_2012Metric_NOLBL; LCSC C84260
Q1321, Q1322: 2N7002; SOT-23-N; LCSC C8545
R1, R3, R5, R7, R9: 1K; R_0603_1608Metric_NOLBL; LCSC C21190
R2, R4, R6, R8: 20K; R_0603_1608Metric_NOLBL; LCSC C4184

Connections:
+5V: D1.2 (A), D2.2 (A), D3.2 (A), D4.2 (A), D5.2 (A), D6.2 (A), D7.2 (A), D8.2 (A), D9.2 (A)
GND: Q1321.2 (S), Q1322.2 (S)
unnamed: D1.1 (K), R1.1
unnamed: D2.1 (K), R2.1
unnamed: D3.1 (K), R3.1
unnamed: D4.1 (K), R4.1
unnamed: D5.1 (K), R5.1
unnamed: D6.1 (K), R6.1
unnamed: D7.1 (K), R7.1
unnamed: D8.1 (K), R8.1
unnamed: D9.1 (K), R9.1
O: Q1321.3 (D), R2.2, R4.2, R6.2, R8.2
P1: Q1321.1 (G)
P2: Q1322.1 (G)
X: Q1322.3 (D), R1.2, R3.2, R5.2, R7.2, R9.2
