schilkp/Fets_and_Crosses/ECAD/Fets_and_Crosses/KiCad/UI_GameState.sch

## KiCad design ECAD/Fets_and_Crosses/KiCad/UI_GameState.sch (2022-02-07)

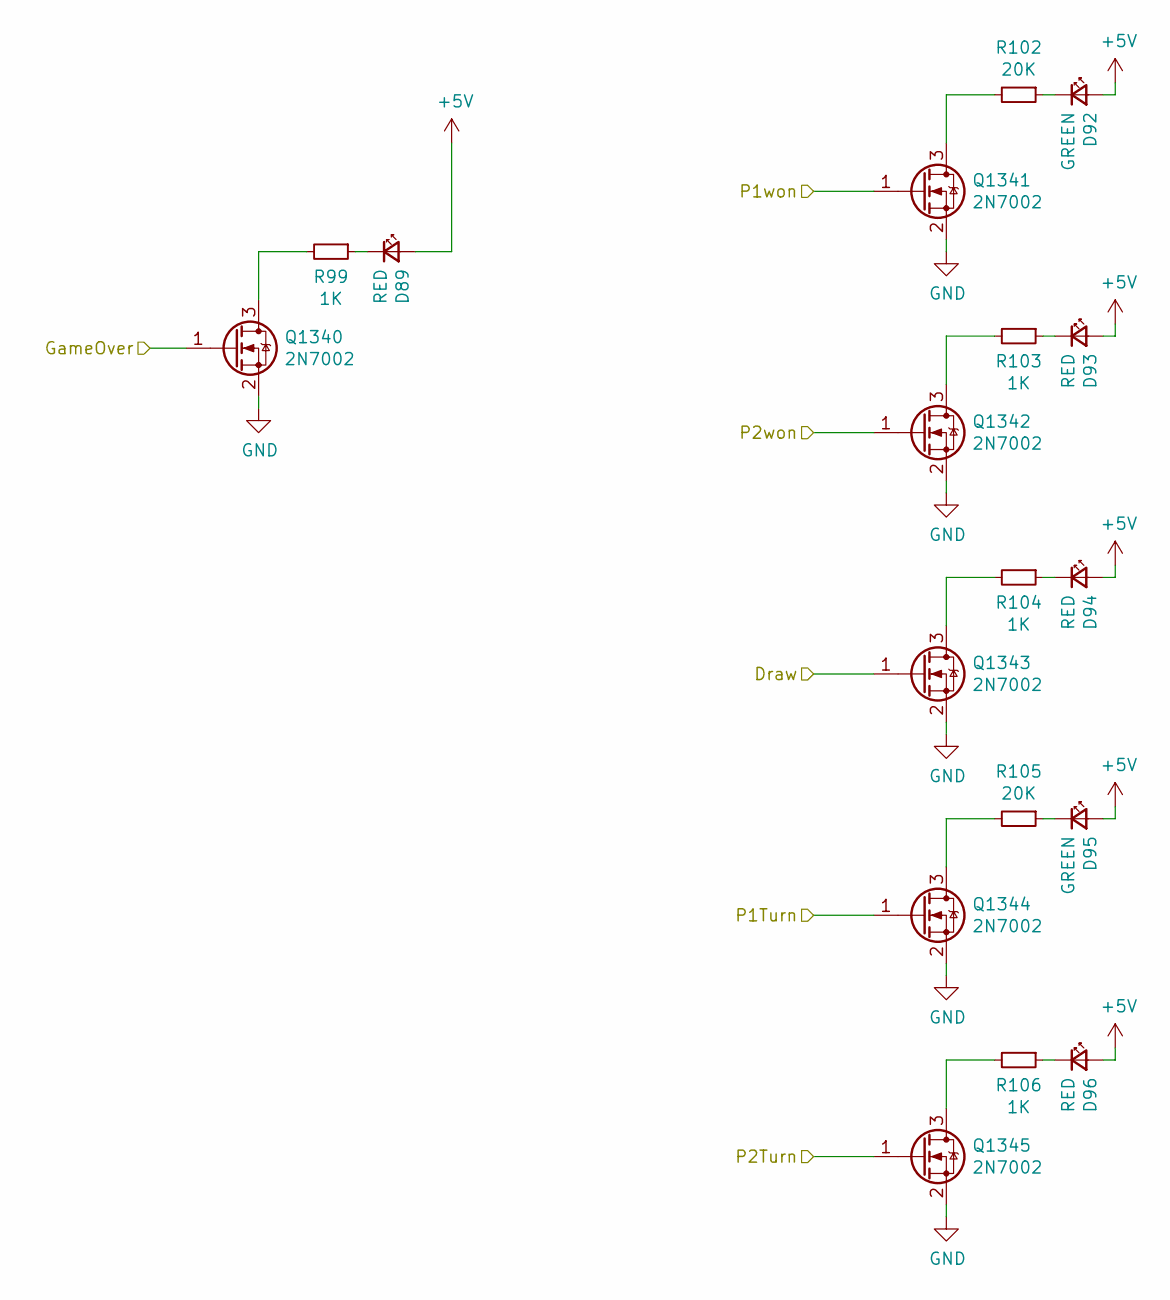
[picture p225: schematic UI_GameState.sch]

Parts:
D89, D93, D94, D96: RED; D_0805_2012Metric_NOLBL; LCSC C72037
D92, D95: GREEN; D_0805_2012Metric_NOLBL; LCSC C84260
Q1340, Q1341, Q1342, Q1343, Q1344, Q1345: 2N7002; SOT-23-N; LCSC C8545
R99, R103, R104, R106: 1K; R_0603_1608Metric_NOLBL; LCSC C21190
R102, R105: 20K; R_0603_1608Metric_NOLBL; LCSC C4184

Connections:
+5V: D89.2 (A), D92.2 (A), D93.2 (A), D94.2 (A), D95.2 (A), D96.2 (A)
Draw: Q1343.1 (G)
GND: Q1340.2 (S), Q1341.2 (S), Q1342.2 (S), Q1343.2 (S), Q1344.2 (S), Q1345.2 (S)
GameOver: Q1340.1 (G)
unnamed: D89.1 (K), R99.1
unnamed: D92.1 (K), R102.1
unnamed: D93.1 (K), R103.1
unnamed: D94.1 (K), R104.1
unnamed: D95.1 (K), R105.1
unnamed: D96.1 (K), R106.1
unnamed: Q1340.3 (D), R99.2
unnamed: Q1341.3 (D), R102.2
unnamed: Q1342.3 (D), R103.2
unnamed: Q1343.3 (D), R104.2
unnamed: Q1344.3 (D), R105.2
unnamed: Q1345.3 (D), R106.2
P1Turn: Q1344.1 (G)
P1won: Q1341.1 (G)
P2Turn: Q1345.1 (G)
P2won: Q1342.1 (G)
