schilkp/Fets_and_Crosses/ECAD/Fets_and_Crosses/KiCad/UI_MoveSelect.sch

## KiCad design ECAD/Fets_and_Crosses/KiCad/UI_MoveSelect.sch (2022-02-07)

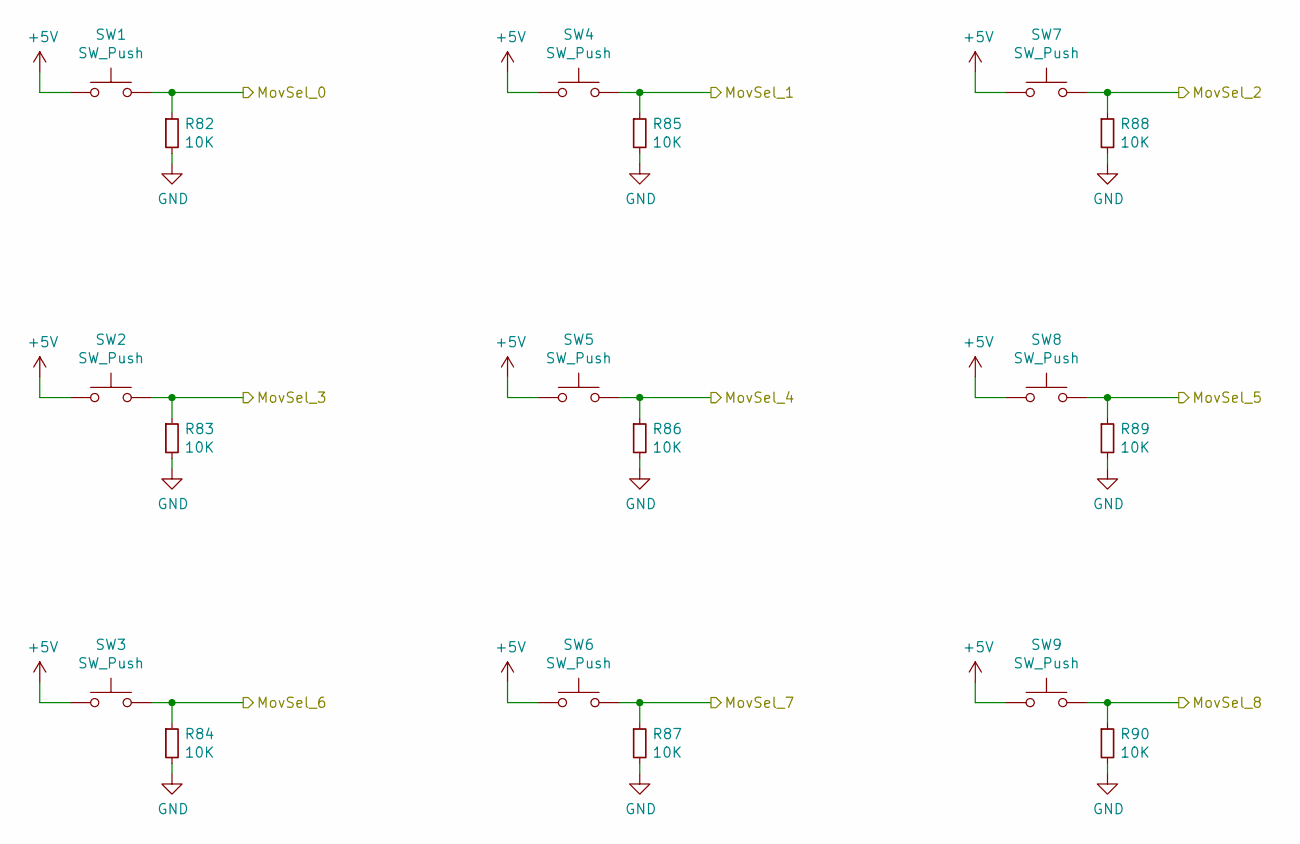
[picture p226: schematic UI_MoveSelect.sch]

Parts:
R82, R83, R84, R85, R86, R87, R88, R89, R90: 10K; R_0603_1608Metric; LCSC C25804
SW1, SW2, SW3, SW4, SW5, SW6, SW7, SW8, SW9: SW_Push; SW_PUSH_6mm

Connections:
+5V: SW1.1, SW2.1, SW3.1, SW4.1, SW5.1, SW6.1, SW7.1, SW8.1, SW9.1
GND: R82.2, R83.2, R84.2, R85.2, R86.2, R87.2, R88.2, R89.2, R90.2
MovSel_0: R82.1, SW1.2
MovSel_1: R85.1, SW4.2
MovSel_2: R88.1, SW7.2
MovSel_3: R83.1, SW2.2
MovSel_4: R86.1, SW5.2
MovSel_5: R89.1, SW8.2
MovSel_6: R84.1, SW3.2
MovSel_7: R87.1, SW6.2
MovSel_8: R90.1, SW9.2
