schilkp/Fets_and_Crosses/ECAD/Fets_and_Crosses/KiCad/UI_Setup.sch

## KiCad design ECAD/Fets_and_Crosses/KiCad/UI_Setup.sch (2022-02-07)

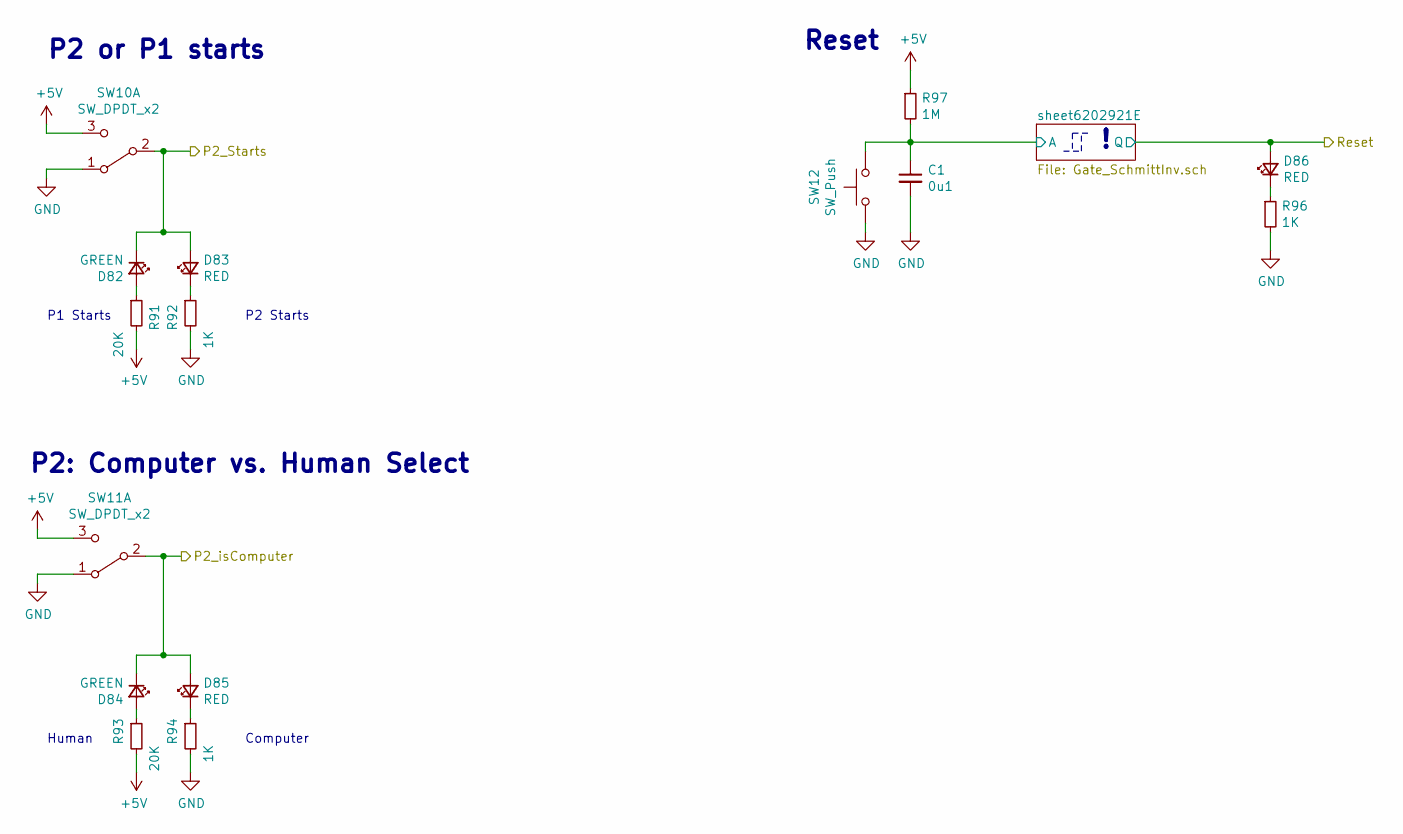
[picture p227: schematic UI_Setup.sch]

Parts:
C1: 0u1; C_0603_1608Metric_NOLBL; LCSC C14663
D82, D84: GREEN; D_0805_2012Metric_NOLBL; LCSC C84260
D83, D85, D86: RED; D_0805_2012Metric_NOLBL; LCSC C72037
R91, R93: 20K; R_0603_1608Metric_NOLBL; LCSC C4184
R92, R94, R96: 1K; R_0603_1608Metric_NOLBL; LCSC C21190
R97: 1M; R_0603_1608Metric; LCSC C22935
SW10, SW11: SW_DPDT_x2; SW_E-Switch_EG1271_DPDT
SW12: SW_Push; SW_PUSH_6mm

Connections:
+5V: R91.2, R93.2, R97.1, SW10.3 (C), SW11.3 (C)
A: C1.1, R97.2, SW12.2
GND: C1.2, R92.2, R94.2, R96.2, SW10.1 (A), SW11.1 (A), SW12.1
unnamed: D82.2 (A), R91.1
unnamed: D83.1 (K), R92.1
unnamed: D84.2 (A), R93.1
unnamed: D85.1 (K), R94.1
unnamed: D86.1 (K), R96.1
P2_Starts: D82.1 (K), D83.2 (A), SW10.2 (B)
P2_isComputer: D84.1 (K), D85.2 (A), SW11.2 (B)
Reset: D86.2 (A)

Notes on the sheet:
P2: Computer vs. Human Select
Reset
P2 or P1 starts
P2 Starts
P1 Starts
Computer
Human
