schilkp/Fets_and_Crosses/Scripts/Engines/engine_hardware_bridge.py

from Utils.get_int import get_int
from Engines.EngineError import EngineError
import serial
import serial.tools.list_ports
import sys
import copy
import re


class engine_hardware_bridge:
    def __init__(self):
        self.com = None
        argv = sys.argv

        self.debug = False
        if len(argv) >= 3:
            if argv[2] == "debug":
                self.debug = True

        pass

    def __str__(self):
        return "engine_hardware_bridge"

    def open(self):
        port_list = serial.tools.list_ports.comports()
        port_count = len(port_list)

        if port_count == 0:
            print("No serial ports found....")
            sys.exit(-1)

        print("%i Serial port(s) found:" % port_count)
        for index, port in enumerate(port_list):
            print("%i: %s - %s" % (index, port.device, port.description))

        if port_count == 1:
            print("Selected port.")
            port = port_list[0].device
        else:
            prompt = "Select port [0-%i]:" % (port_count-1)
            port = port_list[get_int(prompt, range(port_count))].device
            print("Selected port.")
        try:
            self.com = serial.Serial(
                port, 115200, timeout=1.5, write_timeout=1)
            print("Serial port openened.")
        except serial.SerialException:
            print("Failed to open serial port.")
            sys.exit(-1)

    def close(self):
        self.com.close()

    def respond(self, b, current_player):
        # TODO implement engine
        # Return the move the engine should make (0-8), given the current
        # board b. current_player indicates what player you are playing
        # as (1-2)

        if(current_player == 1):
            b = copy.deepcopy(b)
            for i in range(9):
                if b.get_i(i) == 0:
                    continue
                elif b.get_i(i) == 1:
                    b.set_i(i, 2)
                elif b.get_i(i) == 2:
                    b.set_i(i, 1)

        # Construct package:
        package_str = "STATE-"
        for i in range(9):
            package_str += str(b.get_i(i))
        package_str += '\n'

        package = package_str.encode('ascii')

        try:
            self.com.flushOutput()
            self.com.flushInput()

            # Send package
            self.com.write(package)

            # Get reponse
            resp = self.com.readline()
            resp = resp.decode('ascii')

            if not re.fullmatch(r'^RESP-[0-8]\n$', resp):
                print('Did not receive valid response...')
                print('Received: ' + str(resp))
                raise EngineError()

            if self.debug:
                print("%s - Response: %s" %
                      (package_str.rstrip('\n'), resp[5]))

            return int(resp[5])

        except serial.SerialException:
            print('Serial exception...')
            raise EngineError
