schilkp/Fets_and_Crosses/Engine_Tester_Firmware/EngineTester/Inc/TesterErrors.h

/*
 * TesterErrors.h
 *
 *  Created on: Jun 10, 2021
 *      Author: pschilk
 */

#ifndef INC_TESTERERRORS_H_
#define INC_TESTERERRORS_H_

typedef enum {
	TESTER_OK = 0,
	TESTER_ERR = 1
} testererror_t;


#endif /* INC_TESTERERRORS_H_ */
